okchois/Oilinwater/docs/hw/artwork-a5-r2-silk-logo-261003.md

# HMT500 A5-R2 실크 레퍼런스·두텍 로고 (2026-10-03)

## 바뀐 것

- 실제 PCB F.SilkS/B.SilkS와 거버에 반영. PDF에 번호를 덧씌우는 방식이 아니다.
- 표시 레퍼런스 **56 → 92/110개**. 부품 몸체 밖의 가까운 위치로 조정하고 혼동 가능 위치는 짧은 지시선(26개)을 사용했다.
- 기본 문자 폭/높이/선폭 **0.5/0.8/0.1 mm**. 혼잡 위치 22개는 **0.4/0.6/0.1 mm**로 축소.
- 탑면 J1 뒤쪽 빈 공간에 원본 **DOTECH 워드마크 폭 8.0 × 높이 1.34 mm**. 인쇄 가독성을 위해 작은 부제는 생략. 모델명은 로고 아래에 배치.
- 로고는 원본 알파 윤곽을 벡터로 변환한 실제 실크 다각형이다.
- 회로·부품 위치/면/회전·패드·배선/비아는 유지. 최신 LCSC 매칭 BOM/CPL을 새 거버 묶음에 포함.

## 검사

전체 재생성: 넷리스트 81/81 일치, DRC 오류 0, 미연결 0, 테스트 33개 통과.
실크 겹침 경고 0. **작은 글씨 높이 경고 22개** 및 기존 C44/D1 라이브러리 차이 경고 2개는 공개하고 유지한다.
이전 판과 배선/비아·패드의 형상/넷 및 부품 위치·회전·면 동일을 프로그램으로 대조했다.
탑/보톰 PDF는 실제 실크+마스크 개구+외곽이며, 보톰은 뒤집어서 읽는 방향이다.

## 남은 위험

**모든 레퍼런스를 실크로 표시한 것은 아니다.** 아래 18개는 가까운 공간에서 패드/몸체/다른 번호를 피하는 배치를 확보하지 못해 숨겼다:

D51, U13, U15, U2, C28, C4, C44, C45, C48, C50, C55, FB1, R14, R19, R31, R51, R52, R9

0.6 mm 적용 번호: D40, D41, L3, U1, U10, U9, C2, C21, C30, C41, C46, C5, C52, C57, GDT1, R11, R15, R17, R30, R33, R42, R8.

[JLC 고정밀 문자 안내](https://www.jlc.com/portal/q6i10417.html)는 최소 높이 0.8 mm·선폭 0.1 mm를 제시한다. 이번 0.6 mm 글씨는 그 권장 한계보다 작으므로 제조사 인쇄성 확인이 필요하며 선명한 인쇄를 보장하지 않는다. 일반 공정은 더 큰 글씨를 요구할 수 있다.

기존 0.15 mm 비아/POFV DFM, CPL 방향·재고, 제품 온도·몰딩·EMC 검증은 남아 있다. 이 자료는 제조 검토용이며 발주 승인이 아니다.

## 자료

- `manufacturing/jlc/artwork_A5_R2_review/`: 실제 거버·드릴, 현재 BOM/CPL, DRC/manifest.
- `hardware/kicad/artwork_metrics.json` 대신 프로젝트 폴더 `hardware/kicad/HMT500(260313A)/artwork_metrics.json`: 각 번호 좌표·크기·숨김 목록.
- 생성기 `silk_layout.py`, `artwork_finish.py`; 로고 원본/벡터는 `hardware/kicad/assets/`.
