okchois/Oilinwater/docs/hw/artwork-a4-261002.md

# HMT500 PCB A4 작업 결과

2026-10-02 · 회로 v0.10 / 기구 Rev I / PCB A4 · **미완성 검토용 — 제작·주문 불가**

## 바뀐 것

6층·신호 비아 축소 이후의 후속 배선을 수행했다. 미연결은 **A3 15건 → A4 5건**으로 줄었지만, 배선 완료 목표는 아직 달성하지 못했다. 기존 A1/A2/A3의 배치·배선 스냅샷은 보존했다. 회로의 부품 110개·넷 81개, 전원 12–28 V, VAO 16.1 V, 부하 조건 및 기구 외형은 변경하지 않았다.

- R42: 기구 좌표 x 44.925→45.475 mm, y 0.425→0.225 mm. GND 연결 및 DAC2 ISET 연결을 다시 배선했다.
- C6: x 18.650→18.600 mm. 최종 코트야드의 왼쪽 끝은 x 16.275 mm로 홀더 제한 x 16.250 mm를 만족한다. 초기 배치 시도에서 발견된 홀더 침범은 최종판에서 수정했다.
- R42 이동에 맞춰 MCU 반대면의 배치 탐색용 예약 창을 A4에서만 축소했다. A3 예약 창은 보존했다. 실제 패드·비아 간격 및 기구 배치 검사는 유지했다.
- eFuse UVLO·OVP·RTN 배선을 다시 정리했다. UVLO 인출 비아는 최종 KiCad 좌표 (108.500, 99.825) mm이다. CHASSIS 윗면 배선은 eFuse 옆에서 국부적으로 우회하며, 1.0 mm 간격을 유지한다.
- 고립된 GND와 3.3 V 구간을 연결했다. In2/In3에 디지털 영역의 3.3 V 폴리곤을 추가했다. In1/In4에는 신호 배선을 넣지 않았다.
- ADC PT_N과 인접 PT_SN_F 경로를 함께 조정했고 DAC 통신선 등 여러 신호를 재연결했다. 남은 막힌 경로는 아래 표와 그림에 표시했다.
- 신호 비아 0.30/0.15 mm 82개, 전체 관통 비아 220개이다. 기타 비아는 0.35/0.20, 0.40/0.20, 0.45/0.20, 0.70/0.40 mm이다. 블라인드·매립 비아는 사용하지 않았다.

## 확인한 것

| 검사 | 최종 결과 |
|---|---|
| 생성기부터 회로·PCB 재생성 | 성공, 종료 코드 0 |
| 넷리스트 | 81/81, 오류 0 |
| PCB 패드–넷 대조 | 오류 0 |
| 구리층 / GND 기준면 | 6층 / In1·In4 신호 배선 없음 |
| CREF·벅 SW/FB·DAC CMP 배선 길이 제한 | 통과 |
| 테스트 | 33개 통과 |
| KiCad 10.0.6 일반 DRC 오류 | 0 |
| **KiCad 미연결** | **5건 — 아래 상세** |
| DRC 경고 | 배선 끝 미연결 25건, 라이브러리 차이 2건 |
| 기구 조립 시뮬레이션 재실행 | 31항목: NG 0, WARN 1 |

DRC 경고는 제외하지 않았다. 라이브러리 차이는 기존 C44/D1의 실크를 Fab으로 옮긴 데서 발생한다. 배선 끝 경고와 미연결 항목은 별도의 집계다. 기구 WARN은 몰딩 유동/잔류 기포를 CAD로 보장할 수 없다는 항목이다. 이 결과는 원본 패드–넷 검사이며 KiCad의 네이티브 회로도 대조 오류 0을 주장하는 것은 아니다.

## 남은 위험

**전원 VIN_P와 RS-485 A, SWCLK, OUT1_SGOOD가 완전히 연결되지 않았다. 따라서 정상 동작 또는 제작 가능 상태가 아니다.** 임시 점퍼, ERC/DRC 제외 규칙, GND 기준면 침범으로 미연결을 숨기지 않았다.

| 미연결 | 의미 / 다음 처리 |
|---|---|
| VIN_P 1건 | eFuse 출력 측과 VAO 벅 입력 측 전원 연결. MCU/DAC 중앙 구간에서 전원 통로를 먼저 확보해야 한다. |
| RS485_A_EXT 2건 | U11 A핀–D60 TVS–J1 사이의 세 구간이 분리되어 있다. U11/D60 인출과 커넥터 방향 경로를 함께 수정해야 한다. |
| SWCLK 1건 | MCU U4.36–SWD J2.4 연결. MCU 우측 핀 탈출과 기존 비아 위치를 재검토해야 한다. |
| OUT1_SGOOD 1건 | 보호 IC U9.8–MCU U4.11 연결. MCU 왼쪽 탈출부와 반대면 DAC 주변의 배선 여유가 필요하다. |

단순 우회·주변 배선 제거 후 복원·배선 잠금 해제 등을 시험했으나 위 5건을 모두 해소하지 못했다. 연결 수가 다시 늘거나 간격 오류가 생긴 시험판은 최종판으로 채택하지 않았다. 이후 작업은 막힌 부품 인출부의 배치와 주변 경로를 함께 바꾸어야 한다. 다음 작업자에게 이 5건을 넘긴 것이 완료를 의미하지 않는다.

- SMD 패드와 비아 외경의 겹침을 보수적인 패드 경계 상자로 검사한 **POFV 후보는 22개**다. 모두 홀 0.20 mm 이상이며, 0.15 mm 홀 후보는 0개다. 실제 마스크·페이스트·제조 공정 확인은 별도로 필요하다. `POFV_candidates.csv`에 좌표를 기록했다.
- JLC 공개 POFV 범위는 홀 0.20–0.50 mm, 권장 환형 링 0.075 mm이다. [JLC 공식 POFV 안내](https://jlcpcb.com/news/free-via-in-pad-6-20-layer-pcbs-pofv). **0.15 mm 일반 비아와 0.20 mm POFV 혼용의 최종 제조 수락·가격은 확인 필요**이며 현재 파일만으로 해당 공정을 주문한 상태는 아니다.
- RTN 채움 구리의 계산 면적은 F.Cu 약 19.01 mm², B.Cu 약 20.05 mm²다. 패드/배선 자체의 구리까지 합산한 열 모델이 아니므로 방열 성능 보장에 사용할 수 없다. eFuse 시동·고장·최고 온도 시험이 필요하다.
- 배선 연결을 모두 마친 뒤 전원·서지 경로의 좁아진 곳, GND 귀환 경로, AO 발열, 디커플링 루프를 검토해야 한다. 일반 DRC 오류 0만으로 전기 성능 검수를 마친 것은 아니다.
- 제조 DFM·최종 적층 두께·BOM 미확정 2줄·CPL 회전·실장 공정은 주문 전에 확인해야 한다. 거버와 JLC 주문 패키지는 발행하지 않았다.

## 내가 결정할 것

이번 6층·비아 축소 작업은 이미 승인받은 범위이며 추가 승인을 요구하지 않는다. 현재는 주문 승인 단계가 아니다. 기존 제품 온도·몰딩 재료 등의 미결 사항은 결정 기록을 유지한다.

## 재현

`hardware/kicad/rebuild_artwork.sh`의 기본은 A4다. `placement/artwork_A4.json`과 `routing/artwork_A4_draft.json`이 배치·배선의 입력이며, 층수나 배치가 다르면 스냅샷 복원을 거부한다. 이전 판은 HMT_ARTWORK=A1/A2/A3로 지정한다. 검토 묶음에는 생성기·라이브러리·회로/PCB·검사 결과를 포함했다. 데이터시트 PDF는 포함하지 않았다.

## 미연결 상세 — KiCad 좌표 mm

| # | 넷 | 시작 | 끝 |
|---|---|---|---|
| 1 | OUT1_SGOOD | 배선 [OUT1_SGOOD] on B.Cu, 길이 0.8202 mm (135.337, 106.175) | 패드 11 [OUT1_SGOOD]의 U4 위F.Cu (124.138, 102.250) |
| 2 | SWCLK | 패드 36 [SWCLK]의 U4 위F.Cu (132.463, 97.250) | 배선 [SWCLK] on F.Cu, 길이 0.1414 mm (107.850, 97.000) |
| 3 | RS485_A_EXT | 패드 6 [RS485_A_EXT]의 U11 위F.Cu (117.025, 106.200) | 배선 [RS485_A_EXT] on B.Cu, 길이 0.2750 mm (116.575, 107.000) |
| 4 | RS485_A_EXT | 배선 [RS485_A_EXT] on B.Cu, 길이 0.6500 mm (118.525, 107.275) | 패드 3 [RS485_A_EXT]의 J1 위F.Cu (139.650, 101.875) |
| 5 | VIN_P | 배선 [VIN_P] on B.Cu, 길이 1.0645 mm (133.700, 107.640) | 배선 [VIN_P] on In2.Cu, 길이 0.1750 mm (118.325, 101.750) |
