okchois/Oilinwater/docs/hw/ao-tvs1401-261001.md

# AO TVS1401 변경 — 회로도 v0.10 / 결정 #41

사용자 지시에 따라 D30/D40만 TVS3301DRBR → TVS1401DRBR로 변경했다. 입력 D2, RS-485 D60/D61은 33 V 부품을 유지한다. VAO 16.1 V, TPS26611, 10 Ω 직렬 저항, 출력 부하 ≤500 Ω 및 최대 24 mA는 유지한다.

- 정상 부하 단자전압: 24 mA × 500 Ω = 12 V. 0–10 V 출력과 함께 ±14 V 스탠드오프 범위 안이다. 14 V는 정확한 클램프 전압이 아니다.
- TI SLVSEQ2B §8.6: 30 A, 8/20 µs에서 클램프 전형 20.5 V / 최대 22.2 V(27°C, 초기 0 V), 최대 23.55 V(125°C, 초기 ±14 V).
- 단순 검산: DAC측을 +16.1 V로 가정하고 단자 −23.55 V이면 TPS26611 양단은 39.65 V. ±55 V 절대최대보다 낮지만 VAO 공차·IN측 순간전압·배선 오버슈트·파형/전류/온도는 별도 확인해야 한다. 실제 서지 시험 통과를 뜻하지 않는다.
- IN 핀 1–4, GND 5–8. 노출 중앙 패드는 반드시 FLOAT. 기존 Texas_DRB0008A_PadFloat 풋프린트를 유지한다.
- **AO 단자에 외부 ±28/30 V 지속 인가 무손상 보장은 제외한다.** 외부 전원→TVS→GND 경로는 TPS26611 및 10 Ω 바깥에 있어 이 부품들이 그 전류를 차단하지 못한다.
- 출력 개방 시 DAC의 컴플라이언스 전압 상승으로 TVS가 연속 도통할 수 있다. 24 mA 개방 상태의 TVS 온도·SGOOD/DAC 경보·펌웨어 개방 검출을 시험해야 한다. 보호가 개방 검출에 미치는 영향도 확인 필요.
- LCSC C1849891로 BOM을 분리했다. JLC 조립 등급·재고·가격은 주문 시 확인 필요.

근거: [TI TVS1401 데이터시트](https://www.ti.com/lit/ds/symlink/tvs1401.pdf), [LCSC C1849891](https://www.lcsc.com/product-detail/C1849891.html). 제조사 PDF는 커밋하지 않았다.

검증: AGENTS §5 재생성 순서 완료, unittest 33개 모두 통과, 넷리스트 81/81 오류 0. PCB 부품 배치 좌표 유지. D30/D40 TVS1401 2개(C1849891), D2/D60/D61 TVS3301 3개(C2864392)로 BOM 분리 확인. DRC 간격·코트야드 오류 0. 기존 실크/라이브러리 항목 426, 미연결 327(배선 전)은 남아 있다. PCB/넷리스트 재생성은 Mac KiCad 10.0.6으로 수행했다. 회로도 표제란 v0.10 및 AO 오결선 보장 제외 주석을 PDF에서 확인했다.
