okchois/Oilinwater/docs/hw/mcu-selection.md

# MCU 선정 검토 — HMT500

작성일: 2026-09-26 · 상태: **결정 — STM32G0B1CCT3** (샘플 단계는 JLC 부품 CCT6, 결정 #39 — 양산 전 온도 사양으로 재확인) (2026-09-26, 사내 사용 부품 우선 방침). T3 견적 확인 대기

현재 회로도는 STM32L431RCT6(LQFP64, −40~85 °C)입니다. 이 문서는 "이 칩이 최선인가"를 요구사항부터 다시 따져 봅니다. 끝에 다른 AI 도구(Codex CLI 등)나 외부 검토자에게 그대로 넘길 수 있는 질문지를 붙였습니다.

> 표의 가격과 온도 등급은 공개 자료와 기억에 기댄 값입니다. **대리점 견적과 데이터시트로 반드시 확인**해야 합니다. "확인 필요" 표시가 붙은 항목은 특히 그렇습니다.

## 0. 두텍 MCU 사용 이력 (구매현황 2023-09 ~ 2026-09 기준)

| 부품 | 코어 | 적용 제품 | 구매 경로 | 단가 수준 (참고) |
|---|---|---|---|---|
| STM32F412RET6 | M4F 100 MHz, 512 KB | HPX3000 | Mouser | 약 9,200~9,900원 |
| STM32G071CBT6 (LQFP48) | M0+ 64 MHz, 128 KB | PSU750, GTX500 | Mouser | 약 3,300~3,600원 |
| **STM32G0B1CCT6 (LQFP48)** | M0+ 64 MHz, **256 KB** | **DP2000** | **국내 대리점**, Mouser | **약 2,060원 (100개, 국내)** |
| STM32G031K6T6 (LQFP32) | M0+ 64 MHz, 32 KB | GTX30P | Mouser | 약 2,600원 |
| STM32L011F3/F4U6 | M0+ 32 MHz, 8/16 KB | HTP1100W | DigiKey | 약 1,200원 |
| (STM32F103VET6) | M3 | 구매현황 제목에만 있음, 기간 내 구매 행 없음 | — | — |

**정리:** 두텍은 STM32만 쓰고, 특히 **G0 계열(G031, G071, G0B1)** 을 여러 제품에 쓰고 있습니다. L4와 G4는 쓴 적이 없습니다. M4F는 F412를 HPX3000에 씁니다. **STM32G0B1CC는 같은 부품을 DP2000에 쓰고 있고 국내에서 사고 있어서**, 개발 도구, 드라이버, 생산 기록 지그, 재고를 함께 쓸 수 있습니다.

## 1. MCU가 해야 할 일 (요구사항)

| # | 요구 | 근거 | 필수/선호 |
|---|---|---|---|
| R1 | SPI 1개, 칩 선택 4개 (PCAP04, ADS1220, DAC8760 ×2) | 회로 설계서 6절 | 필수 |
| R2 | UART 1개 + RS-485 방향 제어(DE). 하드웨어 DE면 더 좋음 | Modbus RTU 3.5문자 간격, 부트로더 | 필수 (HW DE는 선호) |
| R3 | GPIO 약 20개 (인터럽트 2, 알람·고장 입력 5, LED 1, SWD 2 포함) | 핀 할당표 | 필수 |
| R4 | 플래시 ≥ 128 KB, 가능하면 256 KB. 페이지 단위 소거 | 부트로더 32K + 앱 + 설정 + 교정 | 필수 |
| R5 | 실수 연산: ppm = aw × 10^(A + B/T), 5계수 모델, 교정 다항식 | 측정 주기 약 1 Hz | 선호 (아래 참고) |
| R6 | **동작 온도 −40~105 °C 이상**, 가능하면 125 °C | 오일 최대 120 °C, 전자부 발열 약 1.3 W | 필수 (열해석 후 확정) |
| R7 | 작은 패키지 (7×7 이하) | PCB 폭 23 mm, 한 면 높이·면적 제한 (기구 Rev C) | 선호 |
| R8 | 워치독, 저전압 리셋, 하드웨어 CRC | 현장 무인 동작, 부팅 시 이미지 검증 | 필수 (CRC는 선호) |
| R9 | 국내 수급, 10년 이상 공급, 두텍 개발팀 경험 | 양산·유지보수 | 필수 |
| R10 | 단가 (1k 기준) | 전자부 BOM $36~64 목표 | 선호 |

**R5 다시 보기:** 측정 주기가 약 1 Hz라서 FPU가 꼭 필요하지는 않습니다. FPU 없는 Cortex-M0+도 소프트웨어 실수 연산으로 1초에 한 번 계산하는 데는 충분합니다(코드가 수 KB 늘어나는 정도). 처음 선정 이유에서 "FPU가 필요하다"는 말은 과했고, "있으면 편하다"가 정확합니다.

## 2. 후보 비교

| 후보 | 코어 / 클럭 | 플래시 | HW RS-485 DE | 125 °C 등급 | 패키지 (작은 것) | 단가 감 (1k) | 비고 |
|---|---|---|---|---|---|---|---|
| **STM32L431CC** (현재 계열, 48핀) | M4F / 80 MHz | 256 KB, 2 KB 페이지 | 있음 (USART DEM) | 접미사 3/7 있는지 **확인 필요** | UFQFPN48 7×7, LQFP48 | 약 $2~3 | 부트로더 맵·핀표 그대로 사용. 가장 적은 변경 |
| STM32G491CE/CC (2A절) | M4F / 170 MHz | 512 / 256 KB | 있음 | **있음 (CET3·CEU3 판매 확인)** | LQFP48, UFQFPN48 7×7 | 약 $5~6 (100개) | 요청 후보. 125 °C 확실, 가격 약 2배 |
| STM32G431CB | M4F / 170 MHz | 128 KB | 있음 | 있음 (접미사 3, **확인 필요**) | UFQFPN48 7×7 | 약 $3~4 | 성능 과잉. 125 °C가 꼭 필요하면 후보 |
| STM32G0B1CB / G071 | M0+ / 64 MHz | 128 KB | 있음 | 있음 (접미사 3, **확인 필요**) | UFQFPN48, LQFP48 | 약 $1.5~2.5 | FPU 없음 (R5는 소프트웨어로 해결). 원가 절감 1순위 |
| STM32U0 / U3 계열 | M0+ / M33 | 64~256 KB | 있음 | **확인 필요** | 작은 패키지 다수 | **확인 필요** | 신규 계열. 수급·장기 공급 확인 필요 |
| TI MSPM0G3507 | M0+ / 80 MHz (수학 가속기 MATHACL) | 128 KB | **확인 필요** | 있음 (−40~125 °C) | VQFN32/48 | 약 $1 안팎 | 저가·고온. TI 부품(DAC8760, THVD2450)과 한 대리점. 툴체인 경험 확인 필요 |
| Renesas RA4M1 / RA2L1 | M4F / M23 | 256 KB | **확인 필요** | 제품별 상이 | LQFP48 | 약 $2~3 | 국내 지원 있음. 선택 이유가 약함 |
| GigaDevice GD32 (STM32 호환) | M4F 등 | 다양 | 있음 | 제품별 상이 | 다양 | 저가 | 호환성·장기 공급·품질 문서가 약함. 산업용 계측기에는 비추천 |

## 2A. 요청 후보: STM32G491CET3 상세 검토

주문 코드 해석: G491 · **C** = 48핀 · **E** = 플래시 512 KB · **T** = LQFP48 7×7 · **3** = −40~125 °C (접합 130 °C).

| 항목 | STM32G491CET3 | STM32L431CC (비교) | HMT500에서 의미 |
|---|---|---|---|
| 코어 | Cortex-M4F 170 MHz, CORDIC·FMAC 가속기 | Cortex-M4F 80 MHz | 둘 다 충분. 성능은 G491이 과잉. CORDIC은 지수·로그 계산에 쓸 수 있지만 필요하지는 않음 |
| 플래시 / RAM | 512 KB / 112 KB | 256 KB / 64 KB | 512 KB면 **A/B 두 이미지 업데이트**(실패 시 이전 펌웨어로 복귀)가 가능. 지금 부트로더 맵(256 KB)도 그대로 들어감 |
| 플래시 페이지 | 2 KB (카테고리 4, 단일 뱅크), 64비트 단위 기록 | 2 KB, 64비트 단위 기록 | **부트로더 포팅이 거의 같음** (`bl_port.h` 함수 3개) |
| 온도 등급 | **125 °C 등급이 실제 판매 중** (CET3, CEU3 확인) | 계열 데이터시트에는 125 °C 범위가 있으나 CC 48핀의 3/7 접미사 판매 여부는 **확인 필요** | **G491의 가장 큰 장점** |
| USART / RS-485 DE | USART 3 + LPUART, 하드웨어 DE 있음 | 있음 | 같음 |
| 아날로그 | 12-bit ADC ×2, DAC ×4, OPAMP, 비교기, CAN-FD | ADC ×1, DAC ×2, OPAMP | 이 제품에서는 대부분 안 씀 (측정은 PCAP04·ADS1220, 출력은 DAC8760) |
| 소비 전류 | 170 MHz 동작 시 수십 mA (클럭을 낮추면 줄어듦) | 저전력 계열 | 외부 전원이라 문제는 아님. 3.3 V LDO 여유와 발열만 확인. 16~48 MHz로 돌리면 충분 |
| 패키지 | LQFP48 7×7 (CET3), UFQFPN48 7×7 (CEU3) | 같음 | 폭 23 mm PCB에 들어감 |
| 가격 (참고) | RS 100개 기준 약 SGD 8.5 / HK$ 50 (약 $6.3) | 약 $2~3 | 1k 견적은 대략 **$2~3 비쌀 것**으로 예상. 대리점 확인 필요 |

**평가**

- **장점:** 125 °C 등급을 확실히 구할 수 있습니다. 오일이 120 °C일 때 전자부 온도가 85~105 °C를 넘을 수 있다는 위험을 칩 선정 단계에서 없앨 수 있습니다. 부트로더와 드라이버는 L4와 거의 그대로 쓸 수 있습니다(같은 STM32 HAL, 같은 2 KB 페이지).
- **단점:** 가격이 약 2배이고, 170 MHz와 풍부한 아날로그 기능 대부분을 쓰지 않습니다.
- **변형안:** 512 KB가 필요 없으면 **STM32G491CC(256 KB)** 의 125 °C 등급이 더 쌀 수 있습니다(주문 코드와 가격 확인 필요). A/B 두 이미지 업데이트를 원하면 CE(512 KB)를 유지합니다.

## 3. 현재 판단 (교차 검토 전)

**(최종 갱신 — 구매 이력 반영) 1순위: STM32G0B1CCT3** (M0+ 64 MHz, 256 KB, 144 KB RAM, LQFP48, −40~125 °C)
   - DP2000에서 쓰는 G0B1CCT6과 같은 칩의 125 °C 등급입니다. 핀·코드·툴체인·생산 지그가 같습니다.
   - 플래시 256 KB, 2 KB 페이지, 64비트 단위 기록이라 **부트로더 메모리 맵(32K + 208K + 8K + 8K)을 그대로** 씁니다. 단, 256 KB판은 뱅크 2개(각 64페이지)라서 뱅크 2의 페이지 번호 지정과 "이중 뱅크 + 프리페치" 에라타를 부트로더 포팅 때 확인합니다.
   - FPU가 없지만 1 Hz ppm 계산은 소프트웨어 실수 연산으로 충분합니다(R5).
   - USART 하드웨어 DE, IWDG, BOR, 하드웨어 CRC가 모두 있습니다.
   - 가격: T6이 국내 약 2,060원(100개)입니다. T3(125 °C)은 이보다 조금 비쌀 것으로 보이며, **국내 대리점에 T3 견적과 재고를 확인**해야 합니다.
   **2순위: STM32G491CET3** — FPU·성능 여유가 필요하거나 A/B 이중 이미지(512 KB)를 원할 때. 두텍은 G4를 써 본 적이 없고 가격이 약 3배입니다.
   **제외: STM32L431** — 두텍 사용 이력이 없고 G0B1 대비 이점이 FPU뿐입니다.

이전 판단 (구매 이력 반영 전):

0. **(갱신) 고온 조건이 확정되거나 L431CC 고온 등급을 구하기 어려우면 STM32G491CET3(또는 CC 256 KB판)를 1순위로 합니다.** 125 °C 등급이 판매 중인 것이 확인되었고, 설계 변경은 L431CC와 비슷하게 적습니다.
1. **추천: STM32L431CC 48핀으로 바꾸기.** 단, 105 °C 또는 125 °C 등급을 구할 수 있을 때만입니다.
   - 부트로더 메모리 맵, 하드웨어 DE, CRC, 핀 할당이 그대로라 설계 변경이 가장 적습니다.
   - 64핀 → 48핀으로 PCB 면적이 약 절반이 됩니다.
2. **L431의 고온 등급을 구할 수 없으면:** STM32G0B1(원가) 또는 STM32G431(성능) 중에서 고릅니다. 둘 다 125 °C 등급이 있는 것으로 알고 있으나 확인이 필요합니다.
   - G0: FPU가 없고 플래시가 128 KB라 부트로더 맵을 128 KB에 맞게 다시 짜야 합니다(부트로더 16~24K + 앱 ~96K).
3. **원가를 가장 중시하면:** TI MSPM0G3507을 평가해 볼 가치가 있습니다. UART의 RS-485 하드웨어 DE 지원 여부와 두텍의 개발 경험이 관건입니다.

**가장 큰 결정 요인은 두텍이 이미 쓰는 MCU 계열입니다.** 기존 제품이 STM32라면 STM32 안에서 고르는 것이 개발·생산·유지보수 모두 유리합니다.

## 4. 교차 검토 질문지 (Codex CLI 등에 그대로 전달)

아래 블록을 그대로 복사해 넘기면 됩니다. 저장소 전체를 볼 수 있는 도구라면 파일 경로도 함께 읽도록 합니다.

```text
역할: 산업용 계측기 하드웨어 설계 검토자.

제품: DOTECH HMT500 오일 내 수분 트랜스미터 (E+E EE364급).
- 측정: IST MK 정전용량 습도소자 → PCAP04 (SPI), Pt1000 → ADS1220 (SPI)
- 출력: DAC8760 ×2 (SPI, 전압/전류 선택), RS-485 Modbus RTU (THVD2450)
- RS-485로 펌웨어를 업데이트하는 자체 부트로더 (플래시 맵: BL 32K, 앱 208K, 설정 8K, 교정 8K, 2 KB 페이지)
- 계산: ppm = aw × 10^(A + B/T), 약 1 Hz
- 전원 12~28 V (v0.8), 전자부 발열 약 1.3 W, 오일 온도 최대 120 °C
- PCB: 57 × 23 mm 1장, 원통 하우징 안. 부품 높이 한 면 5~12 mm
- 참고 파일: docs/hw/mcu-selection.md, docs/hw/hardware-block-design.md,
  docs/hw/circuit-design.md, docs/rs485-bootloader-design.md, firmware/bootloader/

현재 선택: STM32L431RCT6 (LQFP64, −40~85 °C). 검토안: STM32G0B1CCT3 (1순위, 회사가 DP2000에 G0B1CCT6 사용 중, 국내 구매), STM32G491CET3 (2순위), STM32L431CC.
회사 사용 이력: STM32만 사용 (F412, G071, G0B1, G031, L011). L4·G4 사용 이력 없음.

질문:
1. 위 요구사항에 대해 STM32L431이 최선인가? 더 나은 후보가 있다면 이유와 함께.
2. STM32L431CC의 105 °C/125 °C 등급(주문 코드 접미사 7/3) 실제 존재 여부와 패키지.
3. STM32G0B1CCT3, STM32G491CET3(또는 G491CC), TI MSPM0G3507과 비교해 원가·고온·RS-485 하드웨어 DE·플래시 구조·장기 공급 측면의 장단점.
4. FPU 없는 코어로 1 Hz ppm 계산과 5계수 모델을 처리할 때의 실제 부담.
5. 이 요구사항에서 놓친 MCU 관련 위험(ESD, 클럭 정확도와 Modbus 보레이트, 플래시 내구성, 부트로더 안전성 등).
답은 표 하나와 추천 1순위·2순위로 정리하고, 확신이 낮은 사실은 "확인 필요"로 표시할 것.
```

## 5. 결정 후 바꿀 곳

- 회로도: `hardware/kicad/gen_hmt500.py` (MCU 심볼·핀), 넷리스트 재검증
- 핀 할당: `docs/hw/circuit-design.md` 6절
- 부트로더 메모리 맵: `docs/rs485-bootloader-design.md` 3절, `firmware/` (플래시 크기가 바뀔 때만)
- 부품표·원가: `docs/hw/bom.csv`, `docs/hw/bom-cost.md`
- 기구 3D의 MCU 크기: `hardware/mech/hmt500_params.py` `PCB_PARTS`

## 참고 자료

- STM32G0B1CC 데이터시트 (−40~125 °C 등급 포함): https://www.st.com/resource/en/datasheet/stm32g0b1cc.pdf
- STM32G0B1 이중 뱅크·프리페치 에라타 논의: https://community.st.com/stm32-mcus-products-25/dual-bank-issue-on-stm32g0b1rct6-26786
- STM32G491CET3 가격: RS Online https://sg.rs-online.com/web/p/microcontrollers/0330260 , https://hkcn.rs-online.com/web/p/microcontrollers/0330260
- STM32G491CEU3 (125 °C, QFN): https://estore.st.com/en/stm32g491ceu3tr-cpn.html , Mouser https://www.mouser.com/ProductDetail/STMicroelectronics/STM32G491CEU3?qs=CiayqK2gdcKP%2BMERfRJ0Dg%3D%3D
- STM32G491 플래시 구성(카테고리 4, 2 KB 페이지): https://community.st.com/t5/stm32cubeide-mcus/stm32g491-flash-memory-organization/td-p/696784
- STM32G491 데이터시트 DS13122: https://www.st.com/resource/en/datasheet/stm32g491cc.pdf
- STM32L431 데이터시트 (온도 범위): https://www.st.com/resource/en/datasheet/stm32l431cb.pdf
