okchois/Oilinwater/docs/hw/external-review-response-260930.md

# 외부 회로 검수(2026-09-30) 대응 — HMT500(260313A) 회로도 v0.9

검수 대상: `HMT500(260313A)_schematic.pdf` 8쪽 (2026-09-30 오전 판, SHA-256 8146…edca).
두텍 지시: "맞는 것·동의하는 것을 반영" (결정 #35).

검수 PDF 이후 이미 바뀐 것: C22 220 → 330 pF (결정 #33), L2 XGL4030-153 → XGL4040-153MEC, D50 제조사 확정 (결정 #34).

## 1. 항목별 판단과 조치

| ID | 판단 | 조치 (이 저장소) |
|---|---|---|
| H01 음(−) 서지 때 eFuse IN–OUT | 맞음 | **회로 수정:** D2 뒤·U1 앞 직렬 쇼트키 **D3 PMEG10010ELR-QX** (100 V 1 A, 누설 150 nA, LCSC C5361358). D2가 −42.5 V로 잡는 동안 VIN_P +28 V → 약 71 V를 D3가 받음 (100 V 정격). U1 IN은 음전압을 받지 않음. 손실 약 0.45 V × 0.1 A. U1 입력 넷 이름 = VIN_D. UVLO·OVP는 입력 단자 기준 약 +0.45 V 이동 (UVLO ≈ 9.3 V, OVP ≈ 33.1 V — 입력 DC 절대 최대 33 V는 그대로) |
| H02 RS-485 ±1 kV 서지 | 맞음 | **회로 수정:** A·B–GND에 **TVS3301 D60/D61** (±33 V 동작 → ±30 V 오결선 도통 안 함, 최대 42.5 V @ 27 A < THVD2410 ±70 V). 1 kV / 42 Ω 결합 → 최대 약 24 A. U11을 **THVD2410DGKR (VSSOP-8, 핀 배정 같음, LCSC C1858306)** 로 바꿔 자리 확보 |
| H03 보호기 차단 후 피드백 끊김 | 맞음 (조건부) | **회로 추가 (결정 #37, IVS320 AO rev 1.0 방식):** DAC CMP 보상 VOUT–CMP 4.7 nF + CMP–GND 100 pF (SBAS528D 8.3.2), DAC 출력 클램프 BAS70-04 (D41/D51, GND − 0.3 ~ AVDD + 0.3 V). + 펌웨어 F1–F2, 시험 T3 |
| H04 +Vs 클램프 공차 | 부분 동의 → **해소 (결정 #37)** | **최종:** 제너 폴로워(Q1·R50·D50) 삭제, **+Vs = VAO 16.1 V 벅 고정** (15.5–16.6 V, 권장 30 V까지 13 V 여유). _이전 단계(결정 #35): D50 27 V → BZX84C24LT1G_ (22.8–25.6 V, LCSC C43728). VS ≈ 23.4 V, 최악(상한 + 85 °C 드리프트 − VBE) ≤ 26.4 V → +Vs 권장 30 V까지 여유 3.6 V. 하한(−40 °C, 저전류) 약 19.7 V → 출력 단자 최대 전압 사양에 반영 (2절) |
| H05 L2 품번 없음 | 맞음 | 이미 해결 (XGL4040-153MEC, 결정 #34) |
| H06 12 V 허용 부하 | 맞음 | 사양 표 2절 |
| H07 입력 전류·발열 예산 | 맞음 | 예산 표 3절, 펌웨어 F3 |
| H08 IDAC ≤ 250 µA 문구 | 맞음 | 회로도 문구 → "IDAC = 250 µA 고정" |
| H09 전원 OFF 역급전 | 동의 (위험 낮음) | 시험 T6 |
| H10 센서·출력 정확도 | 맞음 | 펌웨어 F5 (PCAP04 구동 주파수), 정확도 예산 4절 |
| H11 온도 등급·기동·고장 복귀 | 맞음 | 5절 (제품 온도 사양 미정 → 두텍 결정 필요), 펌웨어 F4, F6 |

**자리 확보:** 새 부품 3개(D3, D60, D61)를 넣을 자리가 없어 ① U11을 VSSOP로, ② C7(VIN_P 2.2 µF 100 V 1210)을 빼고, ③ 저전압 R·C 37개를 0603 → 0402(LCSC 대부분 Basic)로 바꿨습니다. 100 nF 디커플링(16 V X7R), 1 µF(10 V X7R, 5 V 이하 넷), 22 nF, 20 pF C0G, 10 k/100 k/1 k/10 Ω 저항(50 V). VS_CLAMP(약 24 V) 콘덴서 C46/C53/C56과 정밀·고전압 부품은 0603 이상 유지. 결과: 104개 전부 배치, RS-485 TVS는 U11 A/B 핀에서 1.4–2.5 mm, D3는 U1에서 3.7 mm. C7은 D3가 음의 서지를 막아 VIN_P를 붙잡아 둘 이유가 없어져 뺐고, 벌크 C5 10 µF와 C43 4.7 µF는 그대로입니다.

## 2. 아날로그 출력 허용 부하 (H06) — 제품 사양 초안

가정: 입력 직렬 손실 R1 4.7 Ω + L1 2 × 0.31 Ω + D3 0.45 V, DAC AVDD 직렬 10 Ω, 전류 출력 헤드룸 2 V (DAC8760), TPS26611 RON 최대 12.5 Ω + R30/R40 10 Ω, TPS26611 단자 전압 < +Vs.

| 입력 전압 | VIN_P (추정) | 24 mA 최대 부하 (계산) | 20 mA 최대 부하 (계산) | **사양 (여유 포함)** |
|---|---|---|---|---|
| 12 V | 약 11.1 V | 약 340 Ω | 약 410 Ω | ≤ 250 Ω (아래 식) |
| 18 V | 약 17.2 V | 약 600 Ω | 약 720 Ω | **≤ 500 Ω** |
| 24–28 V | 약 23.2 V 이상 | 약 790 Ω (+Vs 최악 하한 19.7 V가 한계) | 약 950 Ω | **≤ 500 Ω** |

**결정 #37 이후 (AVDD = VAO 16.1 V):** 전원 ≥ 18 V에서 VAO 최소 15.5 V → AVDD 15.2 V → 24 mA 최대 부하 약 528 Ω (≥ 500 Ω 사양 만족, 여유 작음 → 시험 T3). 12 V 입력은 벅이 최대 듀티로 VAO ≈ 10.8 V, AVDD ≈ 10.5 V → 24 mA 약 330 Ω (사양 250 Ω 만족). **0–10 V 전압 출력은 AVDD ≥ 10.5 V 필요 (SBAS528D 표 7) → 12 V 입력에서 경계 — 전압 출력 0–10 V는 전원 ≥ 13 V 권장**으로 사양에 표기.

**확정 사양 (결정 #36, 경쟁사 EE364·MMT162·MMT330과 같은 표기):** 전원 **12–28 V DC (최대 28 V)**, 전류 출력 부하 **RL ≤ 500 Ω** (전원 ≥ 18 V). 18 V 미만은 **RL ≤ (V+ − 6 V) / 24 mA** (12 V → 250 Ω). 계산 한계(24 V 약 790 Ω)보다 여유를 둔 값이며 시험 T3으로 확인. 입력 DC 절대 최대 33 V는 손상 한계로 유지 (동작 범위 아님).

- 전압 출력(0–5 / 0–10 V): 최소 부하와 12 V 입력에서 0–10 V 헤드룸은 DAC8760 데이터시트 값으로 확인 후 표에 넣음 (확인 필요). 시제품 시험 T3에서 측정.
- 입력 DC 절대 최대 33 V (TVS3301), 정상 12–28 V.

## 3. 입력 전류·발열 예산 (H07)

| 부하 | 12 V 입력 | 28 V 입력 | 근거 |
|---|---|---|---|
| 출력 2채널 (24 mA + DAC AVDD 약 3.5 mA + OPA197 약 1.1 mA) × 2 | 약 57 mA | 약 57 mA | VIN_P에서 바로 |
| 3.3 V 부하 (MCU 약 8, RS-485 송신 54 Ω 약 36, 측정부·기타 약 4) 약 48 mA → 5 V 벅 (효율 85 %) | 약 25 mA | 약 10 mA | 5.0 V × 48 mA / 0.85 / VIN_P |
| 전원 감시·TPS26611 (결정 #37 후: 출력부는 VAO 벅 경유 — 28 V에서 입력 전류 약 41 mA로 감소) | 약 1.5 mA | 약 1.5 mA | |
| **합계 (최악: 두 출력 24 mA + RS-485 연속 송신)** | **약 84 mA** | **약 69 mA** | eFuse 제한 148.9 mA (저전류 공차는 확인 필요, ±20 % 가정 시 최소 119 mA) → 여유 ≥ 35 mA |

- 발열 최악: 28 V, 두 출력 24 mA, 단자 단락 → 채널당 약 0.66 W (대부분 DAC), 합계 약 1.3 W + 전원부 약 0.3 W. 몰딩 시제품 온도 시험(미결 항목 "DAC 발열")으로 판단.
- UVLO(입력 약 9.3 V) ~ DAC 최소 전원 사이에서는 MCU만 동작 → 펌웨어 F3.

## 4. 정확도 예산에 넣을 항목 (H10)

- R32/R42 ISET 15 k 0.1 % 25 ppm/K: 교정 후에도 온도 드리프트 최대 약 0.25 % / 100 K (전류 출력 오차 항목).
- Pt1000 2선: 배선 왕복 1 Ω ≈ 0.26 °C. 1회 영점 교정 후에도 하네스 온도 변화분은 남음.
- C22 330 pF C0G ±2 % (LCSC): 절대값은 교정으로 제거, C0G라 온도 변화 작음.

## 5. 제품 온도 사양 (H11) — 두텍 결정 필요

- 부품 최저 등급: **GDT1 Bourns 2035 −55~+85 °C**, JST SH/GH −25~+85 °C (카탈로그, 확인 필요). MCU T3·PCAP04·X7R은 125 °C.
- 결정 필요: 주위 온도 범위, 오일 최고 온도(120 °C)에서 **전자부(몰딩 안) 최고 온도**. 85 °C를 넘으면 GDT·JST 대체품 필요.

## 6. 펌웨어 필수 요구 (검수 반영)

| ID | 요구 | 근거 |
|---|---|---|
| F1 | SGOOD(PA0/PA4)가 High(고장)이면 해당 채널 DAC 출력 끄기(OUTEN = 0) 또는 설정값 유지. 복귀 시 DAC 슬루 제한(SREN) 켜고 천천히 목표값으로 | H03 전압 모드 포화 → 재연결 과도 방지 |
| F2 | 전압 모드 단락·오결선 해제 후 파형으로 슬루 설정값 확정 (시험 T3) | H03 |
| F3 | VIN_SENSE(PB0)로 입력 전압 감시: DAC 최소 전원 미만이면 출력 무효 표시(NAMUR 고장 전류 또는 알람), 히스테리시스 두고 복귀 | H07 |
| F4 | DAC 초기화: 전원 안정 후 리셋 → 출력 비활성 상태에서 설정(REXT = 1, SPI2 모드 3, LATCH 타이밍) → 출력 켜기. 통신 끊김·IWDG 리셋·UVLO 때 출력값 정책을 사양으로 정의 | H11 |
| F5 | ADS1220 IDAC = 250 µA 고정. PCAP04 센서 구동 주파수 약 10 kHz (MK33-W 권장, 확인 필요) | H08, H10 |
| F6 | HSI16 온도 오차: 부팅 첫 프레임부터 UART 허용 오차 만족 확인, 보정 방식 구현·시험 | H11 |

## 7. 시험 계획 추가 (시제품)

| ID | 시험 | 합격 기준 |
|---|---|---|
| T1 | 입력 음(−) 서지: 28 V·경부하·출력 충전 상태, U1 IN–OUT, IN–RTN, OUT–RTN, D3 역전압 차동 측정 (전 온도) | 정격 이내, 손상 없음, 자동 복귀 |
| T2 | RS-485 서지: 결합망 42 Ω, ±1 kV 선–대지·선–선, 극성·횟수 명시 | 손상 없음, 통신 복귀, 오류율 |
| T3 | 출력: 12/24/28 V × 0/20/24 mA × 0/5/10 V, 부하·케이블 용량, 단락·오결선 해제 시 단자·DAC 측 파형 | 과도 한계·복귀 시간 사양 이내 |
| T4 | VAO 16.1 V (결정 #37): −40/25/85 °C, 12–28 V 입력, 기동·차단·부하 스텝 중 전압·리플, 12 V 드롭아웃 동작 | 15.5–16.6 V (≥ 18 V 입력), DAC AVDD ≥ 10 V |
| T5 | 두 출력 최대 부하 + RS-485 연속 송신 + 최대 연산, 12 V: 입력 전류·eFuse 여유, 몰딩 내부 온도 | 제한 미도달, 온도 사양 이내 |
| T6 | 외부 핀 쌍 ±30 V 매트릭스: 전원 OFF / 12 / 28 V × 출력 −30 / 0 / +30 V, 모드·채널별, 전류 제한·유지 시간 기록 | 손상 없음, 복귀 후 오차 사양 이내 |
| T7 | 센서: 온도·배선·몰딩·ESD 후 영점·스팬 변화, 센서 양단 파형 | 정확도 사양 이내 |

## 8. 재검수 때 넘길 자료

저장소 `okchois/Oilinwater` 브랜치 `claude/oil-moisture-transmitter-shji8x`: 회로도 원본(`hardware/kicad/HMT500(260313A)/`), 넷리스트 검사(`hardware/kicad/check_netlist.py`), PCB 배치, 부품리스트(LCSC), `docs/decision-log.md`, `docs/hw/final-review-260313A.md`, 이 문서.
