okchois/Oilinwater/docs/hw/final-review-260313A.md

# HMT500(260313A) 회로 확정 전 3중 검토 + RS-485 몰딩 후 펌웨어 업데이트 검토

작성 2026-09-30 · 대상: 회로도 v0.8 (`hardware/kicad/gen_hmt500.py`), PCB 배치 rev 3 (배선 전)

## 검토 방법

서로 독립된 검토 3회 + 부트로더 검토 1회. 각 검토는 넷을 하나씩 따라가며 제조사 데이터시트 원문과 대조했다.

| 검토 | 범위 | 대조한 원문 |
|---|---|---|
| 1 전원·보호 | M12 입력 → 보호(GDT·TVS·초크) → eFuse TPS26600 → 벅 LMR36006 → LDO → 각 IC 전원, 4–20 mA 출력단, 샤시·접지, 서지·역접속·오배선 | TI SLVSDG2G, SNVSB48C, SLVSFE3C, SBAS528D, SBVS338H, SLVSEG2B, OPA197 |
| 2 측정·MCU | PCAP04, ADS1220 Pt1000, STM32G0B1 핀·AF, SPI 모드, DAC SPI 게이트, RS-485, J1·J2·J3 핀 배정 | TI SLLSF20B, SBAS501D, SBAS528D, ScioSense PCAP04 DS-6, ST 공개 핀 데이터(GitHub XML) |
| 3 일치·제조성 | 심볼 핀 ↔ 풋프린트 패드 ↔ 데이터시트 패키지, 정격(전압·유전체·전력), 넷 무결성, 배치(발열·샤시 간격·배선 가능성) | 위 TI·ScioSense 원문 + KiCad 라이브러리 |
| 부트로더 | 몰딩 후 M12(전원 + RS-485)만으로 펌웨어 업데이트 가능 여부 | TI SLLSF20B, `docs/rs485-bootloader-design.md`, `firmware/bootloader/` |

공통: `check_netlist.py` 74 / 74 넷 일치, `tests.test_kicad_gen` 통과. 막힌 사이트: st.com, littelfuse.com, bourns.com, we-online.com, jst-mfg.com → 해당 값은 "확인 필요".

## 결론

**아직 확정하면 안 됩니다.** 모든 IC의 핀 번호·패드는 데이터시트와 일치하고 회로 구조도 맞지만, 서지·과전압 복귀·벅 입력 콘덴서 등 **몰딩 후에는 고칠 수 없는 항목**이 있습니다. 아래 A는 대부분 부품 1–2개 추가·값 변경으로 해결됩니다.

## A. 확정 전 반드시 고칠 것 (회로)

| # | 문제 | 근거 | 수정 | 검토 |
|---|---|---|---|---|
| A1 | **과전압 차단 후 복귀 안 됨** (U1 TPS26600, R3/R4/R5) | OVP 상승 29.0 V(27.99–30.45), 하강 26.8 V(25.96–27.97) (SLVSDG2G 7.5, 분압비 24.39). 26–28 V 전원에서 핫플러그 링잉·EFT로 한 번 차단되면 전원이 내려갈 때까지 꺼진 채 유지. 공차 하한 개체는 28 V 정상 전원에서도 차단. OVP를 올리면 U9/U10 +Vs(최대 32 V) 초과 | **결정 필요:** (a) 사양을 **12–26 V**로 (회로 변경 없음), 또는 (b) R5 36.5 k (상승 32.6 V / 하강 30.1 V) + U9/U10 +Vs를 VIN_P에서 100 Ω + 27 V 제너 + 100 nF로 분리 | 1 |
| A2 | **음(−) 서지 때 eFuse IN–OUT 역전압 초과** (U1, D2 SMBJ33CA) | IN–OUT 최소 −60 V (−70 V 10 ms). −1 kV 선간 서지에서 D2가 −45…−53 V로 잡는 동안 VIN_P는 +24…28 V(약 17 µF) → IN–OUT −69…−81 V | D2 → **TVS3301DRBR** (이미 BOM에 있음, ±33 V, 42.5 V 클램프) 또는 VIN_F→U1 IN 직렬 100 V 쇼트키(0.4 V 손실). A1과 함께 판단. 몰딩 전 서지 사전 시험 | 1 |
| A3 | eFuse 입력 콘덴서 부족 | SLVSDG2G 11.1: TVS 사용 시 입력 ≥ 1 µF, 12.1: IN 가까이. 현재 C1 100 nF, U1에서 25 mm | **U1 IN(1·2)–GND(9)에 1–2.2 µF 100 V X7R 1210 추가**, D2를 U1 옆으로 | 1 |
| A4 | **벅 LMR36006 입력 콘덴서 없음** (U2) | SNVSB48C 9.2.1.2.6·표 1: CIN 4.7 µF + 220 nF × 2를 "가능한 한 가깝게". 현재 VIN_P 콘덴서(C5, C7)는 U2에서 약 11 mm, 220 nF 없음 | **220 nF 100 V X7R 0603 × 2 (핀 2–1, 10–11) + 4.7 µF 50 V X7R를 U2 옆**. NC 핀 3 → BUCK_SW (데이터시트 권장) | 1·3 |
| A5 | **RS485_DE가 리셋·부팅 중 떠 있음** (U11 DE·/RE 묶음 ↔ PA1) | THVD24x0 표 5-1: DE 내부 2 MΩ 풀다운, /RE 2 MΩ 풀업 → 묶으면 VCC/2 부근(불확정). STM32 핀은 리셋 후 아날로그(부동) → 송신기가 켜져 버스를 막을 수 있음. 11.1항: enable 선 1–10 kΩ 풀업/풀다운 권장 | **RS485_DE – GND 10 kΩ 추가**. 부트로더에도 필수 | 2·부트 |
| A6 | 샤시 저항 R2 정격 (1 MΩ 0603, CHASSIS–GND) | GDT1과 병렬 → 서지 때 수백 V 임펄스. 0603 정격 약 75 V / 과부하 150 V, 패드 간격 0.8 mm | **1 kV 이상 고전압 칩 저항** (HV 1206/2010) 또는 2–3개 직렬 | 1·3 |
| A7 | X5R 콘덴서 (85 °C 한계) | C6, C10 (22 µF), C9, C12 (1 µF), C13, C24 (10 µF), C18, C25 (4.7 µF). 몰딩 + 자체 발열로 85 °C 초과 | **모두 X7R** (LMR36006도 X7R 요구). 1210 이상(C3, C5, C7, C43)은 소프트 터미네이션(에폭시 응력) | 1·3 |
| A8 | **DAC8760 발열** (U7/U8) | 28 V·24 mA 단락 최악 0.73 W/채널, 2채널 1.46 W. θJA 32 °C/W(JEDEC)로도 85 °C 주위에서 TJ ≥ 108 °C, 몰딩 튜브 안은 더 높음. 또 U8은 PCAP04 바로 아래, U7은 ADS1220 옆(보드 반대면) | **결정 필요:** BOOST NPN 자리(SBAS528D 8.4.2, 그림 8-6) DNP로 양 채널 추가 + DAC를 측정부에서 먼 뒤쪽으로 재배치. 몰딩 시제품 발열 시험 | 1·3 |
| A9 | SWD 핀 ERC 오류 (U4 35·36) | 생성기에서 35·36에 no-connect 표시가 붙은 채 J2와 연결됨 → KiCad 넷 이름 `unconnected-(J2-SWDIO)`. PCB 넷은 정상 | 생성기에서 nc 제외 + SWDIO/SWCLK 라벨, 검사기가 `unconnected-*` 다핀 넷을 오류로 | 3 |
| A10 | JST SH/GH 커넥터 −25 °C 정격 (J1, J3) | 부품표 기록 −25~+85 °C, 제품은 −40 °C | JST에 −40 °C 사용 확인 또는 −40 °C 정격 품목 (같은 핀 배정) | 3 |

## B. 확정 전 권장 (회로, 부품 0–2개)

| # | 내용 | 수정 | 검토 |
|---|---|---|---|
| B1 | SGOOD 입력: PC6/PC7이 PB6/PB7과 EXTI 6·7 충돌 + SGOOD High가 2.0–3.0 V라 STM32 VIH(≈2.31 V, 미확인) 경계 | OUT1/2_SGOOD → **PA0(11), PA4(15)** (두 검토가 같은 핀 제안, ADC로도 읽기 가능) | 1·2 |
| B2 | DAC LATCH 선 리셋 중 부동 | DAC1/2_LATCH 10 kΩ 풀업 → +3V3. (선택) CS_ADC·CS_CDC 100 kΩ 풀업 | 2 |
| B3 | RS-485 속도 등급 | THVD2450(50 Mbps) → **THVD2410DR**(500 kbps, 같은 핀) — Modbus 9.6–19.2 kbps, EMC·반사 유리 | 2 |
| B4 | R31/R41 10 k: ±30 V 오배선 때 93 mW, 무전원 때 VIN_P로 역급전 | **100 kΩ** (OPA197 바이어스 pA) | 1 |
| B5 | U12/U13 OPA197 V+ = VIN_P, DAC AVDD는 10 Ω 뒤 → +VSENSE가 AVDD보다 높아질 수 있음 | U12/U13 V+를 DAC1/2_AVDD로 (비용 0) | 1 |
| B6 | 국부 바이패스 부족 | U9/U10 +Vs 100 nF, U3 LDO 입력 1 µF | 1 |
| B7 | DC 바이어스 후 용량 부족 | PCAP04 VDD18 C25 → 10 µF, VDD33 → 22 µF (또는 10 µF × 2) U5 가까이 | 3 |
| B8 | ADS1220 입력 필터 | C27 10 nF **C0G** 명시, (선택) 공통 모드 1 nF C0G × 2 | 2 |
| B9 | 전원 전압 감시 없음 (UVLO 8 V ~ DAC 최소 10 V 사이 동작) | VIN_P 분압(100 k / 10 k) → 남는 ADC 핀 | 1 |
| B10 | 클럭: 크리스털 없음 (HSI16으로 Modbus, −40/+85 °C 여유 얇음) | HSE(PF0/PF1) 또는 32.768 kHz(PC14/PC15) 자리 DNP | 2·부트 |
| B11 | J3 센서선 ESD (PCAP04 HBM ±1 kV) | 저용량·저누설 ESD 어레이 자리 DNP | 2 |
| B12 | 센서 기준 C22 220 pF는 MK33-W mini(200 pF) 기준. MK33-W(300 pF) 채택이면 270–330 pF | 센서 품번 확정 후 값 결정 | 2 |
| B13 | 음(−) 출력 서지 때 TPS26611 IN–OUT 55 V 초과 가능 (에너지는 DAC 전류로 제한, TI 그림 9-14와 같은 구성) | 서지 사전 시험 항목. (선택) 저누설 클램프 자리 | 1 |

## C. 사양 정리 (문서)

- 입력 절대 최대 **33 V DC 연속** (TVS 때문). circuit-design.md의 "60 V까지 보호"·"60 V 1분 시험" 삭제 — 60 V에서는 D2·R1 파손.
- 전류 출력 부하: **12 V 전원에서 ≤ 350 Ω**, 500 Ω은 전원 ≥ 16 V (계산: 12 V에서 24 mA 최대 361 Ω).
- 문서 갱신: circuit-design.md(22 µH → 15 µH, GDT 품번, 최대 부하 전류 ≈ 90 mA, 옛 부품번호), R19 0.02 %(결정 기록의 0.01 % 정정), kicad README의 VERIFY/TBD.

## D. 배치 (배선 전, 배치 승인 전에 고칠 것)

| # | 내용 |
|---|---|
| D1 | J5 샤시 납땜 구멍이 U2(아랫면, 0.6 mm)·U3 +5V(1.3 mm)와 너무 가까움 → 손납땜 때 브리지 → 샤시 절연(GDT·R2) 무력화. **J5 둘레 양면 2–3 mm 동박 금지**, J5 또는 U2/U3 이동 |
| D2 | GDT1·C3·R2를 J5 옆(또는 입력 GND 노드)에 모으고, CHASSIS는 보드 가장자리로 짧고 넓게, 다른 넷과 2 mm 이상. 현재 GDT1 CHASSIS 패드가 R31(OPA197 입력)·U8·C40(DAC REF)과 0.8–0.9 mm |
| D3 | DAC8760 두 개를 측정부(PCAP04, ADS1220, C22, R19)에서 먼 뒤쪽으로 (A8) |
| D4 | 벅 부품(C8, C9, R8/R9/C11, 새 CIN) 핀에 바짝, MCU 디커플링 C14/C15/C20 핀에 바짝, C41을 D30 옆으로 |
| D5 | U1 방열 비아는 EF_RTN 전용 섬에만 (GND 면 금지), U5 EP 페이스트 ≤ 30 % |
| D6 | 풋프린트 라이브러리 이름을 프로젝트 라이브러리로, 누락된 넷 라벨 추가 (KiCad에서 "PCB 갱신" 때 넷 이름 유지) |

## E. 확인된 것 (문제 없음)

- **핀·패드:** STM32G0B1CCT3 LQFP48 전 핀과 AF(SPI1 AF0, SPI2 AF0, SPI3 AF9, USART2 TX/RX/DE AF1), PCAP04 QFN24, ADS1220 TSSOP16, DAC8760 PWP 24핀, TPS26600 PWP(패드 = RTN), LMR36006 RNX(자체 풋프린트 = TI 랜드 패턴), TPS7A20, TPS26611 DDF, OPA197, THVD2450, 74LVC2G32, TVS3301(패드 부동) — 모두 데이터시트와 일치. PCB 패드 넷 = 의도 넷.
- **측정:** PCAP04 플로팅 싱글 모드(PC0/PC1 기준 C22, PC2/PC3 센서, DC 없음), SPI 모드 1, VDD18/VDD33 최소값 충족. ADS1220 기준 250 µA × 4.02 k = 1.005 V(≥ 0.75 V), IDAC 순응 전압 여유, 게인 ≤ 2, SPI 모드 1 전용 버스.
- **출력:** DAC SPI 모드 3 + OR 게이트 SCLK 게이트(그림 8-9), SDO 3상태 35 ns, ALARM 10 k 풀업, DVDD 외부 3.3 V. TPS26611 방향·설정(32 mA 한계·자동 복귀). TVS3301 ±33 V·27 A.
- **전원:** eFuse UVLO 8.6 V / ILIM 149 mA / 돌입 98 mA, RTN 분리(9.3.5.5). 벅 5.02 V, 15 µH / 22 µF × 2 / 20 pF = 표 1. LDO 조건.
- **역접속 −30 V, 모든 핀 쌍 ±30 V 오배선:** 절대 최대 초과 없음 (R31/R41 전력만 B4).
- **RS-485:** 반이중 2선, 내장 페일세이프, 종단 없음(노드로 맞음). **M12 핀 배정 = EE364** (8 V+, 6 GND, 3 A, 2 B, 4/5 OUT).
- 부품번호 84개 중복 없음, 모든 넷 2패드 이상, IC 전원 핀 미연결 없음.

## F. RS-485 펌웨어 업데이트 (몰딩 후)

**가능 — 단, A5(DE 풀다운)와 아래 펌웨어 조건이 있어야 "벽돌 안 됨"을 보장.**

- **방식:** 플래시 앞 32 KB 자체 부트로더(`docs/rs485-bootloader-design.md`), USART2 PA2/PA3 + 하드웨어 DE(PA1 AF1). M12의 전원·RS-485만 사용 → 몰딩 후 BOOT0·NRST·SWD 불필요.
- **ST 내장(ROM) 부트로더는 사용 불가:** USART2를 보긴 하지만 DE(PA1)를 켜지 못해 응답 불가. 옵션 바이트는 nBOOT_SEL = 1, nBOOT0 = 1 유지.
- **벽돌이 안 되는 이유:** 부트로더 영역은 지우지 않고 쓰기 보호(WRP). 펌웨어 헤더를 **마지막에** 기록 → 정전·통신 끊김·손상 이미지면 헤더가 없어 다음 부팅에 부트로더에 머묾 → 다시 업데이트. 다른 하드웨어용 이미지는 하드웨어 ID로 거부. 교정·설정은 펌웨어 영역 밖.
- **추가해야 할 펌웨어 (CRC는 맞지만 멈추는 펌웨어 대비):**
  1. 전원 켠 뒤 약 1 초 복구 창 (고정 19200 8E1 + 저장 설정, 매직 요청에만 반응) — 전원이 M12에 있으므로 전원 재투입으로 항상 진입
  2. 부팅 확인 카운터 (백업 레지스터, 3회 미확인 또는 IWDG 리셋 반복 → 부트로더 유지)
  3. 하드웨어 워치독 리셋부터 동작 (IWDG_SW = 0), 페이지 지우는 사이 갱신
- **옵션 바이트:** RDP 레벨 1 (IAP 가능), 레벨 2 금지. WRP 0–15쪽. BOR 높은 문턱.
- **업데이트 중 4–20 mA:** 들어가기 전 NAMUR 고장 전류(≤ 3.6 mA) 또는 마지막 값 유지(설정). 부트로더에도 DAC 최소 드라이버.
- **남는 위험:** 단일 슬롯(업데이트 끝날 때까지 측정 없음), 업데이트 중 버스 점유(19200 bps에서 약 76 s), 부트로더 자체 버그(몰딩 전에 충분히 검증, 현장에서 부트로더는 갱신하지 않음).

## G. 확인하지 못한 것

- ST 원문(st.com 막힘): HSI16 온도 정확도, USART 수신 허용 오차, VIH, DUAL_BANK·BOOT_LOCK 동작, 에라타 ES0548.
- Littelfuse·Bourns·Würth(막힘): SMBJ33CA/SMDJ36CA 서지 전류, GDT 방전 개시·홀드오버, 초크 DCR·권선 방향, R1 펄스 정격, L2 Isat.
- HTX99R 핀 배정, 센서 프로브 절연 내압(라인–접지 서지가 센서선으로 가는지).
- 몰딩 상태 열저항(시제품 측정 필요), 서지 전류 분배(시뮬레이션 또는 사전 시험), IEC 61326-1 DC 포트 라인–접지 시험 등급(1 kV 또는 2 kV).

## H. 반영 결과 — 회로도 v0.9 · 배치 rev 4 (2026-09-30, 결정 #32)

두텍 결정: 전원 12–28 V 유지, DAC 발열 = 자리 추가 + 재배치, A·B 전부 반영, 펌웨어 업데이트 = 자체 부트로더(결정 #31).

| 항목 | 결과 |
|---|---|
| A1 과전압 복귀 | ✅ R5 36.5 k → OVP 32.6 V / 복귀 30.1 V. TPS26611 +Vs = VS_CLAMP **이미터 폴로워** (Q1 MMBTA06, 베이스 R50 10 k + D50 BZX84C27 → +Vs ≈ 26.3 V 이하, 정상 24 V에서 약 0.7 V 강하, C53 + 핀마다 C46/C56). 재검토에서 첫 안(R50 1 k 직렬)은 +Vs 전류로 2–3.5 V가 떨어져 바꿈 |
| A2 음(−) 서지 | ✅ D2 → TVS3301DRBR, U1 옆 (0.2 mm). 여유는 eFuse IN–OUT 펄스 정격 −70 V / 10 ms 기준. **입력 DC 절대 최대 33 V** (TVS3301이 DC 약 34.5 V 이상에서 손상) |
| A3 eFuse 입력 C | ✅ C2 2.2 µF 100 V X7R, U1 옆 (0.35 mm) |
| A4 벅 입력 C | ✅ C16/C17 220 nF 100 V (U2 핀 0.3 mm), 벌크 = C5 10 µF를 U2 옆으로 (별도 C19는 자리 부족으로 빼고 C5가 겸함), U2 핀 3 = BUCK_SW |
| A5 DE 풀다운 | ✅ R60 10 k |
| A6 R2 | ✅ 1 MΩ 고전압 1206 (품번 확인 필요) |
| A7 X5R | ✅ 전부 X7R (일부 품번 확인 필요) |
| A8 DAC 발열 | ⚠️ DAC를 측정부에서 떼어 x 42–48로 재배치. **부스트 자리는 넣지 못함** — DAC 옆에 두면 ISET-R·REF C·AVDD 부품이 10–20 mm 밀려남. 몰딩 시제품 발열 시험으로 판단 |
| A9 SWD ERC | ✅ no-connect 제거, 검사기가 `unconnected-*` 다핀 넷을 오류로 |
| A10 JST −40 °C | ⏳ JST 확인 대기 (미결) |
| B1 SGOOD | ✅ PA0/PA4 (EXTI 0·4, ADC 가능). CS_CDC는 PA15로, PB0은 VIN_SENSE |
| B2 풀업 | ✅ R10/R11 10 k (LATCH), R12/R13 100 k (CS) |
| B3 THVD2410 | ✅ |
| B4 R31/R41 | ✅ 100 k |
| B5 OPA197 V+ | ✅ DACn_AVDD, C45/C55 |
| B6 국부 C | ✅ C46/C56 (+Vs), C26 (LDO 입력) |
| B7 PCAP04 C | ✅ C25 10 µF, C24 22 µF 10 V (1206 X7R) |
| B8 C27 | ✅ 10 nF C0G (공통 모드 C는 선택 — 넣지 않음) |
| B9 전원 감시 | ✅ R14/R15/C30 → PB0 |
| B10 크리스털 | ⚠️ 넣지 못함 (MCU OSC 핀 옆 자리 없음) → HSI 공장 트림 + 펌웨어 보정 |
| B11 센서선 ESD | ⚠️ 넣지 못함 (J3 옆 자리 없음) → 프로브 ESD 시험 후 |
| B12 C22 | ✅ 센서 MK33-W (300 pF) 확정(결정 #33) → C22 330 pF C0G 1% |
| D1 J5 | ✅ 가장자리 쪽(y 7.4)으로, 구멍 중심 ~ 코트야드 3.3 mm 양면 금지 (재검토: 2.5 mm는 코트야드 간격 1.15 mm뿐이라 늘림) |
| D2 샤시 부품 | ⚠️ CHASSIS 넷클래스 간격 1.0 mm(몰딩 안)·선폭 0.5, 부품 간격 +0.5 mm. 재검토 후 GDT1·C3·R2를 입력 보호부(U1·D2) 쪽 앞 구역으로 모음 → MCU·DAC·OPA197과 떨어짐. J5 패드까지 11–17 mm (J5 둘레 금지 구역 때문에 더 붙일 수 없음) → 배선 때 CHASSIS 전용 굵은 선 |
| D3 DAC 위치 | ✅ 측정부에서 약 5 mm 이상 |
| D4 핀 옆 부품 | ✅ 배치기에 **핀 지정 배치**("pin", IC, 핀번호) 추가. 패드 중심 거리: 벅 C16/C17 1.7–2.5 mm, DAC ISET R32/R42 1.7, REF C40/C50 2.1–2.2, DAC +3V3 C44 2.2, TPS26611 +Vs C46/C56 2.1–2.5, MCU C14/C20/C15 = U4 핀 4–6 바로 아래 아랫면 0.8–2.9 (윗면은 J3 하네스 통로). ⚠️ 남은 것: 벅 BOOT C8 5.4·VCC C9 6.2 mm (J5 금지 구역·U1 사이), U8 +3V3 C54 7.8 mm (핀 2가 가장자리 D1 옆) — 배선 때 짧은 전용 선 |
| D5 RTN 섬·EP 페이스트 | ⏳ 배선 때 |
| D6 라이브러리·라벨 | ⏳ 배선 전 정리 |

검증 (재검토 반영 후): 넷리스트 77/77 일치, 테스트 32개 통과, 조립 시뮬레이션 23항목 NG 0, 부품 84 → 102 (전부 배치, 윗면 38 / 아랫면 64).
