okchois/Oilinwater/docs/hw/humidity-sensor-selection.md

# 습도 센서 선정 — IST AG 정전용량식

작성일: 2026-09-29 · 대상: HMT500 오일 수분 (aw) 측정 · 자료: IST 제품 페이지·데이터시트 요약 (검색 결과. ist-ag.com은 이 환경에서 직접 열리지 않음)

## 1. 요구 조건

| 항목 | HMT500 요구 | 근거 |
|---|---|---|
| 측정 범위 | 0–100 % RH (aw 0–1) | 오일 포화 근처까지 |
| 오일 온도 | −40 ~ **+120 °C** | 설계 목표 (EE364: 80 °C / 옵션 100 °C) |
| 내화학성 | 광유·합성유·에스테르유, 첨가제 | 오일 속 상시 침지 |
| 크기 | 보호캡 Ø9 센서실, 캐리어 폭 4.5 mm 안 | 기구 Rev C (캐리어 9.5 × 4.5) |
| 측정 회로 | PCAP04 (정전용량), 기준 C 220 pF C0G | 회로도 v0.3 |
| 접속 | 4핀 (HTX99R 커넥터 검토 중, 2.54 격자) | 결정 #11 |

## 2. 후보 비교

| 제품 | 용량 (30 % RH, 23 °C) | 온도 범위 | 최대 이슬점 | 크기 | 특징 | 오일 적합성 |
|---|---|---|---|---|---|---|
| **MK33-W mini** | 200 pF ± 40 | **−40 ~ +190 °C** | +95 °C | **5.0 × 3.81 × 0.4/1.2 mm**, 선 10 mm | 응답 t63 < 6 s, 히스테리시스 < 2 % RH | **IST가 오일용으로 권장.** 고온·내화학성 |
| MK33-W | 300 pF ± 40 | −40 ~ +190 °C | +95 °C | 10.8 × 3.81 mm, 선 10 mm | 감도 0.45 pF/% RH, 직선성 < 2 % RH, 측정 주파수 1–100 kHz (권장 10 kHz) | 오일용 권장. 캐리어(9.5 mm)보다 김 |
| P14 Rapid-W | 140 pF ± 40 | −80 ~ +150 °C | +85 °C | 소형 | 빠른 응답, 기상용 (라디오존데) | 온도는 되지만 오일 내화학성 언급 없음 |
| P14-W / P14 Classic | (P14 계열) | 약 −40 ~ +150 °C (확인) | — | 소형 | 범용 | 범용. 오일 전용 아님 |
| HYT 271 (MK33 탑재형) | 디지털 I²C, 공장 교정 | 모듈 −40 ~ +125 °C (확인) | — | 모듈 | ±1.8 % RH, ±0.2 °C. IST 오일 평가키트에 사용 | 센서는 MK33. 모듈 전자부 때문에 125 °C 한계 |
| HYT 939 | 디지털 I²C | −40 ~ +125 °C | — | TO 캔 | ±1.8 % RH, ±0.2 °C | 공기용. 오일 침지 비권장 |

## 3. 선정

### 1순위: **MK33-W mini (200 pF)**

- **오일용 센서입니다.** IST가 MK33을 오일 측정용으로 권장하고, 190 °C까지 쓸 수 있으며 내화학성이 가장 좋습니다. 120 °C 목표에 충분한 여유가 있습니다.
- **크기가 맞습니다.** 5.0 × 3.81 mm라서 캐리어(9.5 × 4.5)에 Pt1000과 함께 올라갑니다. 일반 MK33-W(10.8 mm)는 캐리어보다 깁니다.
- **회로를 바꿀 필요가 없습니다.** 기준 커패시터 220 pF C0G가 센서 용량(200 pF)과 비슷해서 PCAP04 비율 측정에 맞습니다.
- 두텍이 이미 공급받는 "IST MK 센서"와 같은 계열입니다. 공급 품번이 MK33-W mini인지 확인해 주세요.

### 대안: **HYT 271 MK33 (디지털 모듈)**

- 공장 교정된 I²C 출력이라 PCAP04, ADS1220, Pt1000, 기준소자가 빠집니다. 전자부 원가가 약 $10~14 줄고 교정 공정도 단순해집니다.
- 신호가 4선(VDD, GND, SDA, SCL)이라 **HTX99R 4핀 커넥터와 그대로 맞습니다.**
- 대신 모듈 전자부의 최고 온도가 약 125 °C라 120 °C 운전에는 여유가 거의 없습니다. 정확도(±1.8 % RH)도 EE364 수준에 겨우 맞습니다.
- → 오일 최고 온도를 100 °C 이하로 정하면 원가 절감안으로 검토할 가치가 있습니다.

## 4. 설계 반영 사항

| 항목 | 내용 |
|---|---|
| PCAP04 기준 C | 220 pF C0G ±1 % 유지 (MK33-W mini 200 pF). 일반 MK33-W(300 pF)로 바꾸면 270~330 pF로 변경 |
| 측정 방식 | PCAP04 방전시간 측정. IST 권장 교류 주파수(1–100 kHz)와 방식이 다르므로 초기 시험에서 누설·분극 영향 확인 |
| 커넥터 핀 배정 (HTX99R 4핀) | 습도 2핀 + Pt1000 2핀 → **Pt1000이 2선식이 됨** (현재 회로는 4선식). 리드 저항 오차 보정 필요 또는 핀 수 재검토 |
| 교정 | aw 기준점(포화염 또는 습도발생기) + 오일 온도 보상. 공급 로트별 C30 편차(±40 pF)는 1점 교정으로 제거 |

## 4A. 원문 스터디 후 추가 (2026-09-29)

두텍이 제공한 데이터시트·응용노트·백서로 확인한 내용은 [IST MK33 스터디](../reference/ist-mk33-study.md)에 정리했습니다. 핵심은 네 가지입니다.
- **MK33-W mini의 주문 코드는 150138**입니다(백서).
- **최대 이슬점이 95 °C**입니다. 그래서 120 °C에서는 aw 0.43까지만 측정할 수 있고, 사양서에 이 한계를 적어야 합니다.
- **DC 바이어스 없는 교류(1–100 kHz)로 측정**해야 합니다. PCAP04 구동 방식이 이 조건을 만족하는지 확인해야 합니다.
- **온도 보정은 필수**입니다. 보정하지 않으면 100 °C에서 10 % RH 이상 틀어집니다. 교정은 납땜 후 5일이 지난 뒤에 합니다.

## 5. 확인 요청

1. 현재 공급받는 IST MK 센서의 정확한 품번 (MK33-W / MK33-W mini / 기타)
2. 오일 최고 온도 목표 (120 °C 유지 여부) — HYT 271 모듈안 판단용
3. HTX99R 커넥터 4핀 배정 — Pt1000 2선식 허용 여부

## 참고 자료

- MK33-W: https://www.ist-ag.com/en/products/capacitive-humidity-sensor-mk33-w
- MK33-W mini: https://www.ist-ag.com/en/products/capacitive-humidity-sensor-mk33-w-mini-200pf-40-pf
- MK33-W 데이터시트: https://www.ist-ag.com/sites/default/files/downloads/DHMK33-W_E.pdf
- P14 Rapid-W: https://www.ist-ag.com/en/products/capacitive-humidity-sensor-p14-rapid-w-140pf-40-pf
- Moisture in oil Eval Kit (HYT271 MK33): https://www.ist-ag.com/en/products/moisture-oil-eval-kit
- HYT 939: https://www.rapidonline.com/ist-ag-hyt-939-digital-humidity-temperature-sensor-50-9443
