okchois/Oilinwater/docs/reference/ee364-summary.md

# E+E EE364 원문 확인 요약 (구조 참고 제품)

출처: 사용자 제공 PDF — **Datasheet EE364 v1.13 (07-2026)**, **Quick Guide EE364 v3.7 (08-2025)**. 원본 PDF는 저작권 문제로 저장소에 넣지 않았습니다.

> EE364는 구조 참고용 E+E 상용 제품이며 두텍 제품이 아닙니다.

## 1. 치수 (G½ ISO형, mm)

| 항목 | 값 | 해석 |
|---|---|---|
| 전장 | **140** | 프로브 끝 ~ 커넥터 끝 |
| 노출 프로브 | **34** | 프로브 끝 ~ 나사 시작 (필터캡 Ø12) |
| 나사 | G½ | 길이 = 140 − 92 − 34 = **14** |
| 씰면 ~ 커넥터 끝 | **92** | |
| 씰면 ~ 하우징 끝 | **77** | 커넥터 돌출 약 15 |
| 육각 | **AF27** | 씰면 바로 뒤 |
| 하우징 외경 | **Ø30** | 도면상 단차가 있는 원통 (앞쪽 Ø30 → 가운데 조금 가는 부분 → 끝단 칼라) |
| 프로브 외경 | **Ø12** | 측면 구멍 2열 × 4개 |
| NPT형 | ½" NPT, AF22, 노출 51, 나사면 뒤 89 (하우징 끝까지 74) | |

## 2. 사양

| 항목 | EE364 |
|---|---|
| 측정량 | aw, 수분 함량 x [ppm], T |
| aw 정확도 (20 °C) | ±0.02 aw (0–0.9), ±0.03 aw (0.9–1). k=2 불확도 포함 |
| ppm 범위 | 0–100 000 ppm (오일 의존), ppm 출력은 0–100 °C에서 유효 |
| 온도 정확도 | ±0.2 °C (20 °C, 오일 중), 분해능 0.01 °C |
| 응답시간 | 오일 점도와 유속에 크게 의존 (사용자 매뉴얼 그래프) |
| 오일 온도 | −40~+80 °C / 옵션 HM2 −40~+100 °C |
| 주위 온도 | −40~+60 °C / −40~+80 °C |
| 압력 | **0–20 bar** |
| 재질 | 하우징·필터캡 SUS 1.4404 (316L) |
| 보호 등급 | **IP65** / NEMA 4X |
| 아날로그 출력 | 4–20 mA × 2, **3선식**, RL < 500 Ω, 분해능 2 µA, 측정값·스케일 자유 설정 |
| 디지털 | RS-485 (1 unit load), Modbus RTU, FLOAT32 |
| 전원 | **10*–28 V DC** (*최소 = 10 V + 0.02 × RL), Class III |
| 소비전류 | < 20 mA + 부하 전류 |
| 커넥터 | M12×1 8핀 |
| EMC | EN (IEC) 61326-1, 61326-2-3 산업 환경, FCC Part 15 Class B |
| 증명서 | DIN EN 10204-3.1 검사 성적서 기본. ISO 17025 교정 성적서 옵션 |
| 설정 | PCS10 무료 소프트웨어 + Modbus 설정 어댑터(M12↔USB, HA011013) |

### 주문 옵션

- 공정 연결: G½ ISO(PA1) / ½" NPT(PA2)
- 센서 보호: LeadsShield(C2, 리드 보호), ChemShield(C4, 오일 열화·에스테르유 대응 코팅), 둘 다(C6)
- 필터: 유속 < 1 m/s용(F13) / > 1 m/s용(F18)
- 출력 1·2 측정값과 스케일: 기본값 OUT1 aw 0–1, OUT2 T −20~80 °C
- 단위: SI / US
- ppm 환산 오일 파라미터: 광유 변압기유 기본. 고객 오일은 **오일 2 L를 보내 E+E가 파라미터를 측정**(Oil-ppmcal)하거나, 포화곡선으로 계산(Oil-calc)
- 액세서리: 8핀 M12 소켓, 차폐 케이블(1.5/5/10 m), 샘플링 셀(PN40, DN25)

## 3. 핀 배치 (Quick Guide 원문 확인)

**EE364 표준 (M12 8핀)**

| 핀 | 신호 |
|---|---|
| 8 | 전원 V+ (10–28 V DC) |
| 6 | GND |
| 4 | 출력 1 (4–20 mA) |
| 5 | 출력 2 (4–20 mA) |
| 3 | RS485 A |
| 2 | RS485 B |
| 1, 7 | 결선도에 없음 (미사용) |

**EE364 OEM Style (RS485 전용, M12 5핀)**

| 핀 | 신호 |
|---|---|
| 1 | V+ |
| 3 | GND |
| 4 | RS485 A |
| 5 | RS485 B |

- 차폐 케이블 사용이 EMC 조건입니다.
- Quick Guide에는 선색이 나오지 않습니다(이전 문서의 선색은 검색 인용이었으며 표준 M12 케이블 색 기준).

## 4. Modbus (Quick Guide)

| 항목 | 값 |
|---|---|
| 공장 설정 | **9600 bps, 8E1, 주소 243** |
| 선택 가능 | 9600 / 19200 / 38400 / 57600 / 76800 bps, 패리티 N/O/E, 정지비트 1/2, 주소 1–247 |
| 통신 설정 레지스터 | 주소 0x00 (Modbus 주소), 0x01 (통신 설정) — FC06 쓰기 |
| 정보 | 시리얼 번호 ASCII 레지스터 1–8, 펌웨어 버전 레지스터 9, 센서 이름 레지스터 10 |

**측정값 (FLOAT32, FC03/FC04 읽기)**

| 측정값 | 레지스터 번호 (1부터) | 주소 (0부터) |
|---|---|---|
| 온도 T | 26 | 0x19 |
| 수분 활동도 aw | 52 | 0x33 |
| 수분 함량 x [ppm] | 54 | 0x35 |
| 오일 파라미터 A, B, C, D, E | 224, 226, 228, 230, 232 | 0xDF, 0xE1, 0xE3, 0xE5, 0xE7 |

- 오일 파라미터 쓰기(FC16):
  - 구형 방식: A, B만 주소 0x64, 0x66에 씁니다. 이때 C, D, E는 0으로 설정됩니다.
  - 펌웨어 2.0.22 이상: A–E를 0xDF부터 씁니다.
- **FLOAT32 워드 순서는 하위 워드 먼저(CDAB)입니다.** 문서 예시로 확인했습니다.
  - A = −100 → `00 00 C2 C8`
  - B = 7.3705 → `DB 23 40 EB`
- ppm 환산은 5개 파라미터 모델(A–E)입니다. 식 자체는 공개되지 않았습니다(AN0103 확인 필요).

## 5. 우리 설계에 주는 시사점

| 항목 | 반영 |
|---|---|
| 핀맵 | 우리 8핀 안(2: B, 3: A, 4: OUT1, 5: OUT2, 6: GND, 8: V+)이 **EE364와 일치함을 원문으로 확인**. 1, 7번은 EE364에서 미사용이므로 7번 AGND 제안과 충돌하지 않음 |
| 전원 | EE364는 10–28 V. 우리 안은 15–30 V(전압 출력 0–10 V와 전류 출력 부하 때문). 교체 호환을 위해 **최소 전압을 12 V 수준으로 낮출 수 있는지** 검토 (저전압 시 부하 저항 제한) |
| 사양 우위 | 압력 20 → 50/200 bar, 오일 100 → 120 °C, IP65 → IP67, 출력 전류 → 전압/전류 선택, RS-485 펌웨어 업데이트 |
| 정확도 | EE364와 같은 수준(±0.02/±0.03 aw, T ±0.2 °C)이 최소 목표 |
| 교체 호환 모드 | EE364 레지스터(0x19, 0x33, 0x35, 0xDF~), **CDAB 워드 순서**, 공장값 9600 8E1 주소 243을 재현하는 모드. 단, EE364는 주소 0x00이 "Modbus 주소" 레지스터라서, 우리 앱의 0x0000(모드 ID "AP")과 충돌함 → 호환 모드에서는 모드 ID를 다른 주소(예: 0xFF00)로 옮겨야 함. 부트로더·업데이트 도구도 함께 수정 필요 |
| 센서 보호 | ChemShield/LeadsShield에 해당하는 소자 보호 코팅을 IST AG에 문의 (에스테르유·해수 오염 대응) |
| 필터 | 유속별 필터캡 2종(< 1 m/s, > 1 m/s) → 우리 교체형 보호캡으로 대응 |
| 서비스 | 오일 파라미터 측정 서비스(오일 2 L 접수)는 우리도 교정실에서 제공 가능한 사업 요소 |
| 설정 도구 | PC 설정 SW + M 커넥터↔USB(RS-485) 어댑터 → 우리 `fwupdate.py`를 설정·업데이트 통합 도구로 확장 |
