okchois/Oilinwater/hardware/mech/out/HTX99R-SC_sensor_connector.pdf

## 정면도

3 5.5 1.5 1 1.5 5.5

7

15

18

3

### M10×1.0 (바디 체결)

### M10×1.0 (필터 캡)

Ø11

7 (맞변)

홈 Ø8.2 × 1.5

홈 Ø8.1 × 1.5

### C0.5 (양 끝)

## 단면 A-A

7.9

7

2.54

Ø7

### 4× Ø1.5 깊이 7.9, 입구 C0.2

### 4× □0.64 핀, 끝 C0.2

### 오목부 Ø7 깊이 7

## 윗면도 (센서 소켓 쪽)

2.54

2.5

A 4

A

## 아랫면도 (PCB 핀 쪽)

2.54

## 등각도 (참고, 2.5:1)

## 주기 (NOTES)

1. 형상·치수는 두텍 SolidWorks 모델 (HTX99R) Sensor Probe_Sensor Connector.STEP 에서 추출. 단위 mm.
2. 재질·공차·표면처리는 STEP에 없음 — 원 도면 또는 공급사 사양 확인. 일반공차 ISO 2768-mK 가정.
3. Ø10 두 곳은 나사, 위·아래 모두 M10×1.0 (두텍 확인 2026-09-30): 아래 = 바디 체결, 위 = 필터 캡 체결. 윗면 소켓 4× Ø1.5.
4. PCB 풋프린트 제안: 2×2, 피치 2.54, 도금 구멍 Ø1.0, 패드 Ø1.7. 핀 돌출 3.0 → PCB 1.6 t 관통 후 1.4.
5. 홈 Ø8.2 (플랜지 아래): O링 자리 (HMT500은 O링 8×1.2, Ø10 H8 밀봉면). 홈 Ø8.1 (플랜지 위): 위 나사 언더컷.
6. HMT500 Rev F 적용: 바디 앞 M10×1.0-6H 암나사에 체결, 필터 캡을 위 나사에 체결. 아랫면 핀 4× □0.64: 하네스 W-1 납땜 + 수축튜브 (포팅 없음)

# HTX99R-SC 센서 커넥터 — 정면도 · 단면 A-A · 윗면도 · 아랫면도 (5:1, 제1각법)

1 | 2 | 3 | 4 | 5 | 6 | 7 | 8

A

B

C

D

E

F

(주)두텍 DOTECH Co., Ltd. | HMT500(260313) 오일 수분 트랜스미터

품명 센서 커넥터 (HTX99R 센서 프로브)

도번 HTX99R-SC | Rev / 일자 A / 2026-09-29

재질 STEP에 재질 정보 없음 (확인)

척도 5 : 1 | 단위 / 투상 mm / 제1각법

일반공차 ISO 2768-mK

표면(지정 외) Ra 1.6 | 쪽 1/1

작성

### HMT500 설계

검토 | 승인
