okchois/Oilinwater/hardware/mech/out/m12/HMT500_M12_외형도_RevB.pdf

# HMT500 M12 8핀 커넥터 외형도

HMT500-P-204 / Rev B / 2026-10-02 / 기구 Rev I 기준

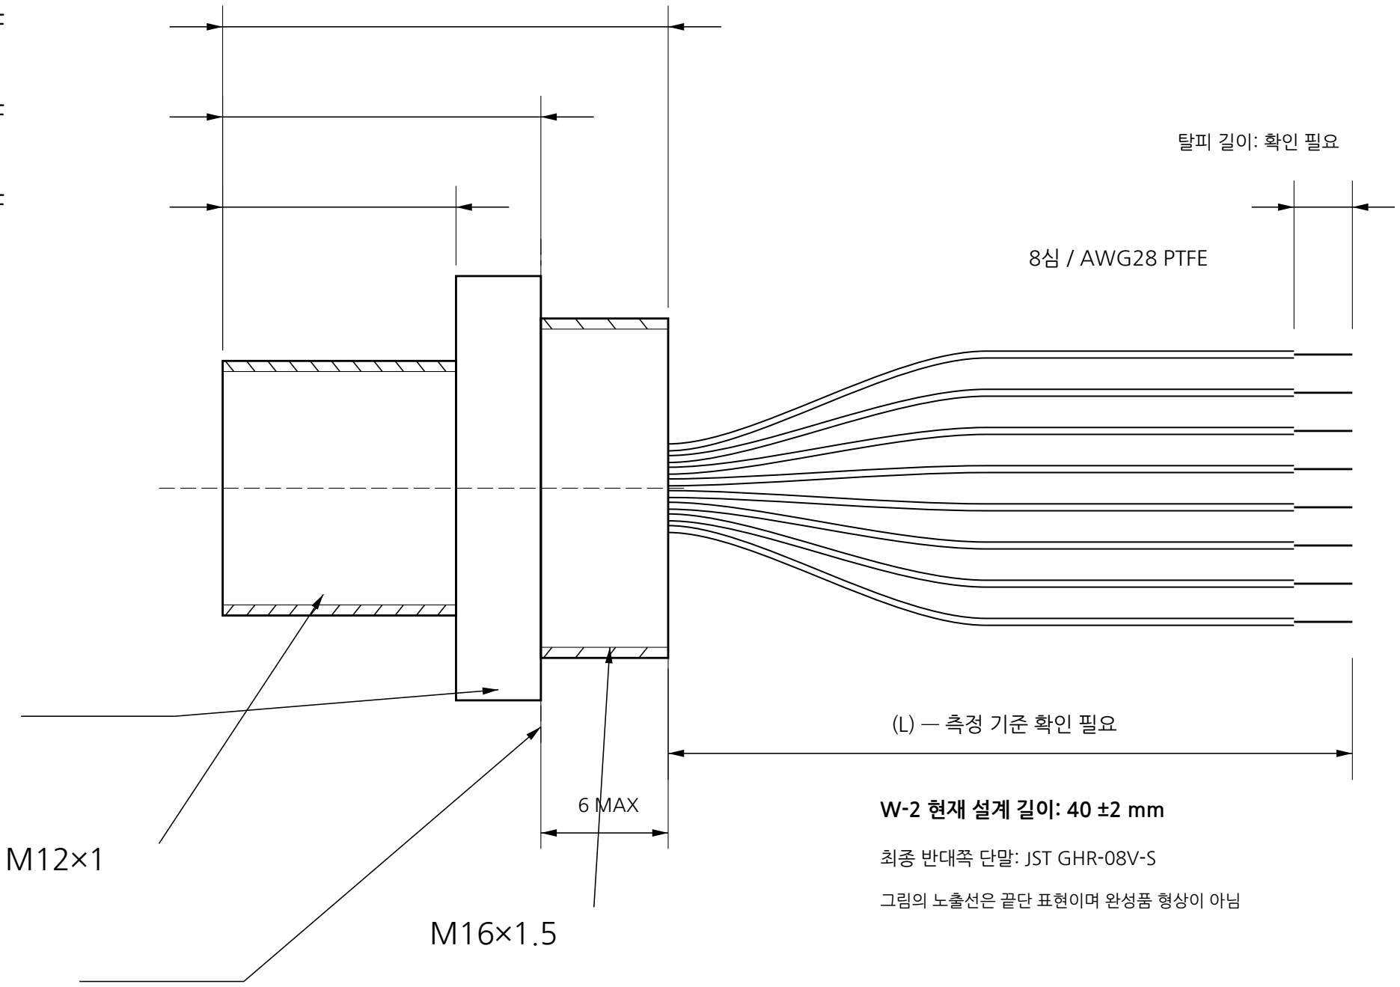
[picture p17: figure]
8심 / AWG28 PTFE; 최종 반대쪽 단말: JST GHR-08V-S; 그림의 노출선은 끝단 표현이며 완성품 형상이 아님; 6 MAX

## 21 REF

## 15 REF

## 11 REF

## Ø20 이하

A: 장착 기준면

### 안쪽 나사부 6 이하

주기: REF는 현 모델 참고치수. 실제 공급사 외형·가스켓·공구 맞변·핀 방향은 품번 확정 후 반영.

A-coded / 8핀 / Male. TURCK 참고 제품의 4핀 T코딩·25.8 mm·탈피 7 mm 치수는 적용하지 않음.

단위 mm / NTS / 선정 검토용 — 제조 승인 아님 | HMT500-P-204-OD / B
