okchois/Oilinwater/hardware/mech/out/m12/HMT500_M12_외형도포함_선정사양서_RevA.pdf

# M12 8핀 커넥터 — 외형·장착 조건

HMT500-P-204 | Rev A | 2026-10-02 | 기구 Rev I / PCB A5-R1
선정·견적 검토용 / 구매품 품번 미확정 / 단위 mm / 축척 없음 (NTS) | 1 / 2

접속부 M12×1과 장착부 M16×1.5는 서로 다른 나사입니다.

장치 내부 | 장치 외부 / 상대 케이블 접속
장착 수나사: M16×1.5 | 접속 수나사: M12×1

형식: A-coded / 8핀 / Male

어깨 외경: Ø20 이하

표현된 외형은 현 기구 모델입니다.

표준이 커넥터 몸체 전체 치수를

정하는 것은 아닙니다.

6 이하 | 4* | 11*

외부 돌출 15*

기준면 A: 엔드캡 뒤 끝면 x=77

* 4 / 11 / 15는 현재 모델 치수이며 선정품 실측값·표준 치수가 아닙니다.

장착 암나사 | 엔드캡 M16×1.5-6H, 모델 x71–77 (길이 6). 구매품 체결·씰 형상 대조 필요.
내부 여유 | PCB 뒤끝 x69 → 모델 커넥터 안쪽 끝 x71: 축 방향 2 mm. 납땜 핀·수축튜브 돌출은 별도.
공구 공간 | 어깨 Ø20 조건에서 M3 경사 주입 공구 여유 0.625 mm. 어깨 확대 시 재검사.
밀봉·고정 | O링/가스켓 형상, 장착 토크, 회전 방지, 체결 유효 길이: 선정품 도면으로 확인 필요.
선정 자료 | 공급사 2D 치수도·STEP·단자 방향도 요청. 안쪽 단자 전체 형상과 외부 돌출 길이를 포함할 것.

# M12 8핀 커넥터 — 전기·하네스·구매 사양

HMT500-P-204 | Rev A | 2026-10-02 | 기구 Rev I / PCB A5-R1
선정·견적 검토용 / 구매품 품번 미확정 / 단위 mm / 축척 없음 (NTS) | 2 / 2

### HMT500 핀 배정 (표준 공통 기능 배정이 아닌 본 제품 배정)

1 | 예비 / PCB NC | → J1.1
2 | RS485_B_EXT | → J1.2
3 | RS485_A_EXT | → J1.3
4 | OUT1_EXT | → J1.4
5 | OUT2_EXT | → J1.5
6 | GND_IN / 전원 | → J1.6
7 | 예비 / PCB NC | → J1.7
8 | VIN_EXT / 전원 + | → J1.8

### 선정 조건 및 현재 상태

접속 형식 | M12 A-coded, 8핀 수형, 직선, 전면 장착
장착 나사 | M16×1.5 (PG9·M16×1 등과 혼용 불가)
제품 사용 전압 | 12–28 V DC / 최대 28 V
커넥터 정격 | 30 V DC 이상 적용 여부 확인; 아래 참고품은 30 V
허용 전류 | 선정품·접점별·배선 규격으로 확인 필요
방수·온도 | 제품 요구와 체결 조건 확정 후 검증; 현재 보증 등급 미확정
하네스 W-2 | 8심 AWG28 PTFE, 현재 40±2 mm, JST GHR-08V-S
단자·배선 | 납땜형 또는 지정 리드선형. 실제 길이·피복·핀별 선색 확인
공통 주의 | 1·7번은 8심에 포함, PCB NC. 샤시는 별도 W-3 연결

핀 배열의 정면/배선면 방향·키 위치는 선정품 제조사 도면을 따릅니다. 본 표를 물리적 핀 위치도로 사용하지 마십시오.

제조사 공식 참고품 — 채택품 또는 무수정 호환품으로 승인한 것은 아닙니다.

[1] Phoenix Contact 1436424 · SACC-E-M12MS-8CON-M16/0,5 P

8핀 Male / A-coded / M16×1.5 전면 장착 / 30 V AC·DC / 2 A / 0.25 mm² 리드선 0.5 m.

현재 W-2의 AWG28·40 mm와 다릅니다. 외형·씰·내부 돌출·JST 압착 적합성을 별도로 확인해야 합니다.

제조사 제품 페이지 및 외형도 열기 [1] (https://www.phoenixcontact.com/en-fr/products/device-connector-front-mounting-sacc-e-m12ms-8con-m16-05-p-1436424)

[2] binder 76 0831 0011 00008-0200 · M12-A series 763

8핀 Male / M16×1.5 / 30 V / 2 A (UL 1.5 A) / 리드선 AWG24·0.2 m. 현재 W-2와 배선 규격이 다름.

제조사 제품 페이지·외형도·접속면 핀 배열 열기 [2] (https://www.binder-usa.com/us-en/products/automation-technology/m12-a/76-0831-0011-00008-0200-m12-a-male-panel-mount-connector-8-unshielded-single-wires-ip68-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)

발행 근거: hmt500_params.py / PCB J1 연결 정보 / 제조사 공식 페이지(2026-10-02 확인). 실제 M Connect 품번: 확인 필요.
