okchois/Oilinwater/hardware/mech/out/harness/HMT500_W-1_RevA.pdf

# HMT500 | W-1 센서 하네스

제작 검토용 · Rev A · 기구 Rev I / PCB A5-R1 기준 · 2026-10-02

### 길이 기준·탈피·압착 조건 미확정 — 양산 제작 승인 도면 아님

## 전기 연결 개략도 (핀 배열도 아님 / 축척 없음)

HTX99R-SC 뒤 납땜 핀 | JST SHR-04V-S → PCB J3
1 | SENS_C1 / MK33 전극 1 | 1
2 | SENS_C2 / MK33 전극 2 | 2
3 | PT_P / Pt1000 | 3
4 | PT_N / Pt1000 | 4

### 배선 사양

4심

AWG30

PTFE (현 설계: UL1213 계열)

기준 설계 길이 Lref

40 ±2 mm

절단/완성 길이 기준: 확인 필요
양단 숫자는 전기적 핀 번호입니다. 실제 커넥터 핀 위치·래치·키 방향을 나타내지 않습니다.

## 구성품

전선 | PTFE AWG30 | 4가닥; 선색 확인 필요
플러그 하우징 | JST SHR-04V-S | 1개
압착 콘택트 | JST SSH-003T-P0.2-H | 4개
맞물리는 PCB 헤더 | JST SM04B-SRSS-TB (J3) | PCB 장착품; 하네스 BOM 제외
납땜부 절연 | 개별 수축튜브 | 4개; 규격·절단 길이 확인 필요

## 제작 치수 확정 항목

Lcut: 전선 절단 길이 — 확인 필요

Lassy: 완성 길이 및 측정 기준점 — 확인 필요

양단 탈피·납땜 길이 — 확인 필요

압착 높이·폭·인장 기준 — 확인 필요

선색·수축튜브 규격 — 확인 필요

## 조립·검사 주기

HTX99R 뒤 핀 납땜 → 바디 통로·홀더 창 통과 → J3에 삽입.

커넥터 체결 중 플러그 끝은 자유롭게 두어 전선 꼬임을 방지.

실제 HTX99R 핀 번호·보는 방향과 대조 후 핀맵 승인.

전수 핀맵 도통·인접선 단락·단자 잠금·납땜부 절연을 확인. 시험 수치와 공구 조건은 해당 단자 사양 확정 후 기입.

도면번호 HMT500-W-001 | Rev A | 단위 mm | A3 / NTS | 1/3 · 작성: 설계 검토
