okchois/Oilinwater/hardware/mech/out/harness/HMT500_W-2_RevA.pdf

# HMT500 | W-2 M12 전원·통신·출력 하네스

제작 검토용 · Rev A · 기구 Rev I / PCB A5-R1 기준 · 2026-10-02

### 길이 기준·탈피·압착 조건 미확정 — 양산 제작 승인 도면 아님

## 전기 연결 개략도 (핀 배열도 아님 / 축척 없음)

M12 8P 뒤 납땜 단자 | JST GHR-08V-S → PCB J1
1 | 예비 / PCB NC | 1
2 | RS485_B_EXT | 2
3 | RS485_A_EXT | 3
4 | OUT1_EXT | 4
5 | OUT2_EXT | 5
6 | GND_IN | 6
7 | 예비 / PCB NC | 7
8 | VIN_EXT / 전원 + | 8

### 배선 사양

8심

AWG28

PTFE (현 설계: UL1213 계열)

기준 설계 길이 Lref

40 ±2 mm

절단/완성 길이 기준: 확인 필요
양단 숫자는 전기적 핀 번호입니다. 실제 커넥터 핀 위치·래치·키 방향을 나타내지 않습니다.

## 구성품

전선 | PTFE AWG28 | 8가닥; 선색 확인 필요
플러그 하우징 | JST GHR-08V-S | 1개
압착 콘택트 | JST SSHL-002T-P0.2 | 8개
맞물리는 PCB 헤더 | JST SM08B-GHS-TB (J1) | PCB 장착품; 하네스 BOM 제외
M12·납땜부 절연 | M12 품번 및 수축튜브 | 품번·치수·절단 길이 확인 필요

## 제작 치수 확정 항목

Lcut: 전선 절단 길이 — 확인 필요

Lassy: 완성 길이 및 측정 기준점 — 확인 필요

양단 탈피·납땜 길이 — 확인 필요

압착 높이·폭·인장 기준 — 확인 필요

선색·수축튜브 규격 — 확인 필요

## 조립·검사 주기

핀 n ↔ 핀 n 직결. 1·7번도 현 8심 하네스에 포함되며 PCB에서는 NC.

밀대로 J1에 삽입할 길이와 턴버클 체결 후 여유선 수납 공간을 함께 확보.

실제 M12 단자·수축튜브 확인 전 길이 축소 금지. 단자 정면/배선면 혼동 주의.

전수 핀맵 도통·인접선 단락·단자 잠금·납땜부 절연을 확인. 시험 수치와 공구 조건은 해당 단자 사양 확정 후 기입.

도면번호 HMT500-W-002 | Rev A | 단위 mm | A3 / NTS | 2/3 · 작성: 설계 검토
