okchois/Oilinwater/hardware/mech/out/harness/HMT500_W-3_RevA.pdf

# HMT500 | W-3 샤시 접지 하네스

제작 검토용 · Rev A · 기구 Rev I / PCB A5-R1 기준 · 2026-10-02

### 길이 기준·탈피·압착 조건 미확정 — 양산 제작 승인 도면 아님

## 전기 연결 개략도 (핀 배열도 아님 / 축척 없음)

PCB J5.1 납땜 | M2 비절연 링 단자 → 바디
1 | CHASSIS | M2 | 배선 사양
| | | 1심
| | | AWG28
| | | PTFE
| | | 녹/황 또는 녹색 (최종 색 확인)

기준 설계 길이 Lref

### 25 mm / 공차 확인 필요

| | | 절단/완성 길이 기준: 확인 필요
양단 숫자는 전기적 핀 번호입니다. 실제 커넥터 핀 위치·래치·키 방향을 나타내지 않습니다.

## 구성품

전선 | PTFE AWG28 | 1가닥
링 단자 | M2 비절연, AWG28 대응 | 1개; 제조사 품번 확인 필요
링 단자 외형 조건 | 바깥 Ø4.5 이하 / 두께 0.8 이하 | 현 기구 설계 조건
체결 위치 | 홀더 위쪽 축 나사 M2×8 | 금속 바디 탭과 전기 접촉
PCB 접속 | J5.1 납땜 | 신호 GND_IN과 혼동 금지

## 제작 치수 확정 항목

Lcut: 전선 절단 길이 — 확인 필요

Lassy: 완성 길이 및 측정 기준점 — 확인 필요

양단 탈피·납땜 길이 — 확인 필요

압착 높이·폭·인장 기준 — 확인 필요

선색·수축튜브 규격 — 확인 필요

## 조립·검사 주기

J5 납땜 → 홀더 위쪽 축 나사의 링 단자 → 금속 바디.

드라이버 접근 경로와 센서 하네스 창을 침범하지 않도록 수납.

링 중심 기준 완성 길이와 전선 절단 길이는 서로 다름. 단자 확정 후 치수화.

전수 핀맵 도통·인접선 단락·단자 잠금·납땜부 절연을 확인. 시험 수치와 공구 조건은 해당 단자 사양 확정 후 기입.

도면번호 HMT500-W-003 | Rev A | 단위 mm | A3 / NTS | 3/3 · 작성: 설계 검토
