okchois/Oilinwater/docs/reference/ist-mk33-study.md

# IST MK33 습도 센서 스터디 — 데이터시트·응용노트·백서 요약과 HMT500 반영 사항

작성일: 2026-09-29 · 원문 (두텍 제공, 저작권상 저장소에는 넣지 않음):
- DHMK33-W_E 2.4.0 — MK33-W 데이터시트 (4쪽)
- AH_E 2.4.0 — Application Note, Humidity Elements (7쪽: MK33, K5, P14, P14 Rapid, 취급·납땜·세척)
- iST White paper "Moisture in Oil" (6쪽, 2023/03)

## 1. MK33-W 데이터시트 핵심

| 항목 | 값 | HMT500에 주는 의미 |
|---|---|---|
| 크기 | 10.8 × 3.81 × 0.4 / 1.2 mm (SIL 선), 0.4 / 0.8 mm (Au/Cu 선) | mini판(5.0 × 3.81)이 캐리어에 맞음 → mini 유지 |
| 습도 범위 | 0–100 % RH, **최대 이슬점 +95 °C** | **고온에서 측정 상한이 줄어듦 (2절)** |
| 온도 범위 | −40 ~ +190 °C | 120 °C 목표에 충분 |
| 기준 용량 C30 | 300 pF ± 40 pF (30 % RH, 23 °C) | 개체 편차 ±13 % → **개별 교정 필수** |
| 감도 | 0.45 pF/% RH (15–90 % RH) | 0–100 % 전 범위 약 47 pF 변화 (284 → 331 pF, 곡선) |
| 손실계수 | < 0.01 (23 °C, 10 kHz, 90 % RH) | 측정 회로의 누설 영향 작음 |
| 직선성 | < 2 % RH (15–90 %, 1점 교정 후) | 저습 쪽이 가파른 곡선 → 다점 교정·다항 보정 권장 |
| 히스테리시스 | < 2 % RH | 정확도 예산의 큰 항목 |
| 응답 t63 | < 6 s (50 → 0 % RH, 23 °C, 공기) | 오일 속에서는 오일 확산이 지배 (4절) |
| 온도 의존성 (공칭) | ΔRH = (B1·RH + B2)·T + (B3·RH + B4). B1 = 0.0011 /°C, B2 = 0.0892 %RH/°C, B3 = −0.0268, B4 = −2.079 %RH | **보정 없으면 오차가 큼** (3절) |
| **측정 신호** | **교류, DC 바이어스 없음, 1–100 kHz (권장 10 kHz), < 12 Vpp** | **PCAP04 구동 방식 확인 필요 (5절, 가장 중요)** |
| 접속 | CuP-SIL 선 Sn 도금 10 mm / Au/Cu 선 Ø0.4 10 mm / Au/Cu 12 mm PTFE 절연 + 실리콘 글롭탑 | 오일 침지 → **PTFE 절연 + 글롭탑판(151306 계열)** 이 유리 |
| 주문 코드 | 150474 MK33 SIL, 150468 MK33-W Au/Cu, 151306 MK33-W HMN300-40.1138.W.012.S (PTFE + 글롭탑) | **MK33-W mini = 150138** (백서) |

## 2. 허용 온습도 범위 — 고온에서 aw 상한

데이터시트의 허용 범위 그래프는 **이슬점 95 °C(수증기압 84.6 kPa)** 가 한계입니다. 95 °C를 넘으면 측정할 수 있는 최대 aw가 줄어듭니다.

| 오일 온도 | 80 °C | 95 °C | 100 °C | 105 °C | 110 °C | **120 °C** | 130 °C |
|---|---|---|---|---|---|---|---|
| 허용 최대 aw | 1.0 | 1.0 | 0.83 | 0.70 | 0.59 | **0.43** | 0.31 |

(포화 수증기압 IAPWS 근사로 계산. 그래프 판독값과 일치)

→ **HMT500 사양 표기:** "aw 0–1 (오일 ≤ 95 °C), 95 °C 초과 시 이슬점 95 °C 이하 범위". 120 °C에서는 aw 0.43까지만 보장됩니다. EE364도 ppm 출력을 0–100 °C에서만 유효하다고 합니다. 펌웨어에서 이 한계를 넘으면 상태 비트와 알람을 켭니다.

## 3. 온도 의존성 보정 (펌웨어)

공칭 식으로 계산한 온도 영향 (23 °C 기준에서 거의 0):

| 온도 | RH 20 % | RH 50 % | RH 80 % |
|---|---|---|---|
| 60 °C | +4.1 % RH | +5.2 | +6.4 |
| 100 °C | +8.5 | +11.0 | +13.5 |
| 120 °C | +10.7 | +13.9 | +17.0 |

- 보정하지 않으면 100 °C에서 **10 % RH 이상** 틀어집니다. 그래서 펌웨어에 이 식을 넣습니다(부호 규약은 IST에 확인).
- 공칭 식이므로, 양산은 **2온도 이상 교정**(예: 25 °C와 80 °C)으로 개체별 계수를 구합니다.
- 측정하는 온도는 습도 센서 바로 옆 Pt1000(MiniSens) 값을 씁니다([온도 센서 선정](../hw/temperature-sensor-selection.md)).

## 4. 백서 — 오일 수분 측정의 원리와 주의점

- **측정 원리:** 오일 속 물이 다공성 윗전극을 지나 고분자층으로 확산되고, 그 물의 양이 정전용량을 바꿉니다. 공기 중과 원리가 같지만, 고온과 첨가제·화학물질 때문에 조건이 가혹합니다.
- **MK33은 오일 수분용으로 특화된 센서입니다.** 다만 상용 오일에는 공개되지 않은 첨가제가 있어서, **오일마다 센서 적합성 평가를 권장**합니다.
- **% RH(aw)가 ppm보다 운전 판단에 낫습니다.** 오일이 노화되면 물 용해도가 바뀝니다. 백서 예시에서는 포화량이 5,000 → 4,000 ppm으로 떨어지면 같은 60 % RH가 3,000 → 2,400 ppm이 됩니다. aw 경보는 노화를 자동 반영하지만 ppm 경보는 여유가 줄어듭니다.
  → HMT500 기본 출력: **OUT1 = aw** (EE364와 같음), ppm은 오일 계수(A, B) 기반 보조 출력. 설정 도구에 이 설명을 넣습니다.
- **평형 시간:** 물이 오일에 고르게 녹는 데는 시간이 걸리고(교반해도 수 시간), 센서 응답보다 훨씬 느립니다. **설치 위치(유동이 있는 곳)** 가 측정 품질을 좌우합니다 → 설치 가이드에 반영.
- **장기 안정성:** 에스테르유·광유에서 장기 측정 결과가 안정적입니다(실온). 변압기 호흡처럼 주위 공기와의 교환이 수분 변동을 만듭니다.
- **관련 IST 제품:** MK33-W mini (150138), HYT 271 모듈 (153382, 공장 교정, I²C), Moisture in oil 프로브 (155958, 완제품).

## 5. 측정 회로 — PCAP04와 "DC 바이어스 없는 교류" 요구 (확인 필요)

- 데이터시트는 **DC 바이어스 없는 교류 신호**로 측정하라고 합니다. 고분자에 DC가 계속 걸리면 물 분자가 이온처럼 이동(분극·전기분해)해 드리프트와 수명 저하가 생길 수 있습니다.
- PCAP04는 센서를 충전 후 저항으로 방전시키는 **방전시간 방식**입니다. 단순 접지형(grounded) 연결에서는 센서에 한 방향 전압이 걸려 평균 DC가 남을 수 있습니다.
- **대책 (우선순위):**
  1. PCAP04를 **플로팅 차동 모드**로 쓰고, 충방전 방향이 번갈아 바뀌는 설정(보상 모드)으로 센서 양단 평균 전압을 0으로 만드는지 ScioSense 자료로 확인
  2. 측정 순간에만 짧게 구동하고 나머지 시간은 센서 양단을 같은 전위로 둠 (듀티 최소화)
  3. 위가 안 되면 10 kHz 교류 구동 + 동기 검파(또는 IST가 쓰는 방식의 전용 ASIC, HYT 모듈)로 변경
- → PCAP04 데이터시트(요청 중) 확인 후 회로를 확정합니다. **미결 사항에 추가.**

## 6. 취급·납땜·세척 (생산 공정 지침에 반영)

| 구분 | IST 지침 |
|---|---|
| 취급 | 활성 면을 만지지 않음. 장갑 필수. **플라스틱 핀셋으로 가장자리나 선만** 잡음 (금속 핀셋 금지). 굽힘·긁힘 금지. UV 노출 금지 |
| 보관 | 원래 블리스터에만, −20 ~ +50 °C |
| 납땜 | 인두 최대 320 °C, 선 끝에서 10 s 이내. 활성 면에 플럭스 잔사 금지 |
| 접착 | 접착제로 고정하면 80 °C × 1 h 베이킹 |
| **교정 시점** | **납땜 후 최소 5일 경과 후 교정** (열 이완 시간) → 생산 일정에 반영 |
| 세척 | 상온 이소프로판올 (약한 초음파 가능) 후 건조. 면봉 등 기계적 세척 금지. 먼지는 오일 없는 여과 공기 |

## 7. HMT500 반영 목록

| # | 항목 | 반영 |
|---|---|---|
| 1 | 센서 품번 | MK33-W mini (150138). 오일 침지를 고려해 PTFE 절연 + 글롭탑 사양을 IST에 문의 (151306의 mini판) |
| 2 | 사양서 | aw 0–1 (≤ 95 °C), 95 °C 초과 시 이슬점 95 °C 한계 (120 °C에서 aw ≤ 0.43) |
| 3 | 펌웨어 | 온도 의존성 보정식 + 개체별 교정 계수, 한계 초과 알람, aw 기본 출력 |
| 4 | 측정 회로 | PCAP04의 DC 바이어스 없는 구동 확인 (5절) — **회로 확정 전 필수** |
| 5 | 교정 | 다점 RH × 2온도 이상, 납땜 후 5일 이후 |
| 6 | 생산 | 6절 취급 지침을 작업 표준서로 |
| 7 | 적용 | 고객 오일별 적합성 시험 절차, 설치 위치 가이드 (유동부) |
