okchois/Oilinwater/hardware/mech/out/assembly_procedure/overview.png

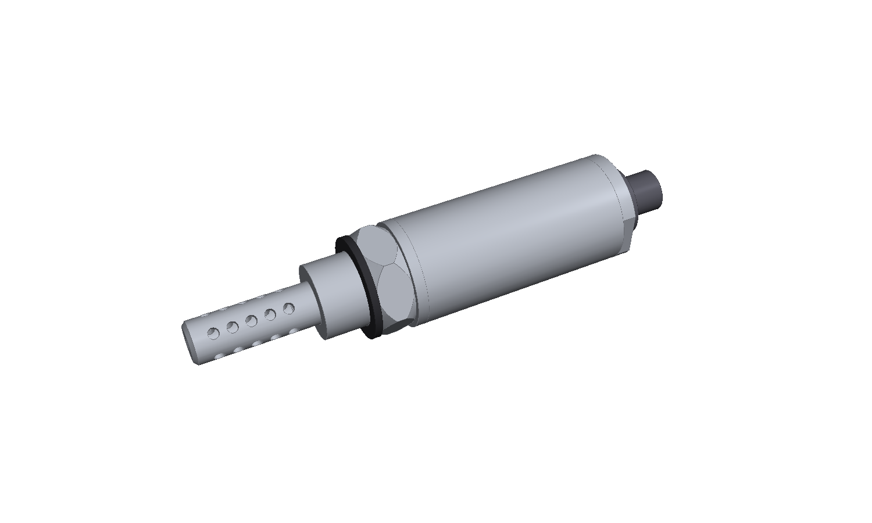
hardware/mech/out/assembly_procedure/overview.png
