okchois/Oilinwater/hardware/mech/out/studio/HMT500_studio_02_rear.png

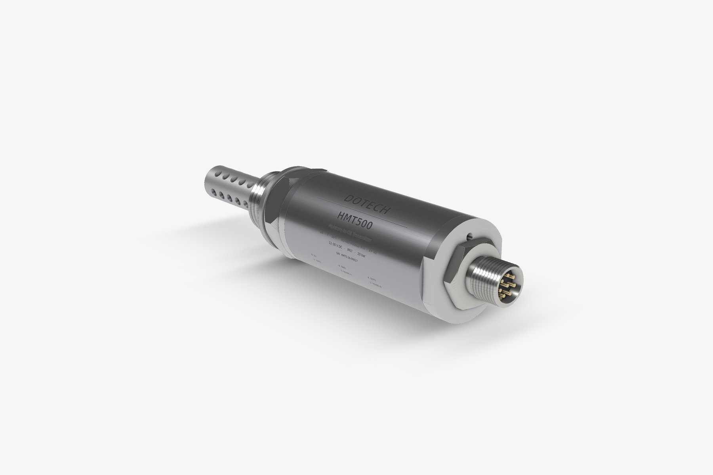
hardware/mech/out/studio/HMT500_studio_02_rear.png
