okchois/Oilinwater/hardware/mech/out/studio/HMT500_studio_03_side.png

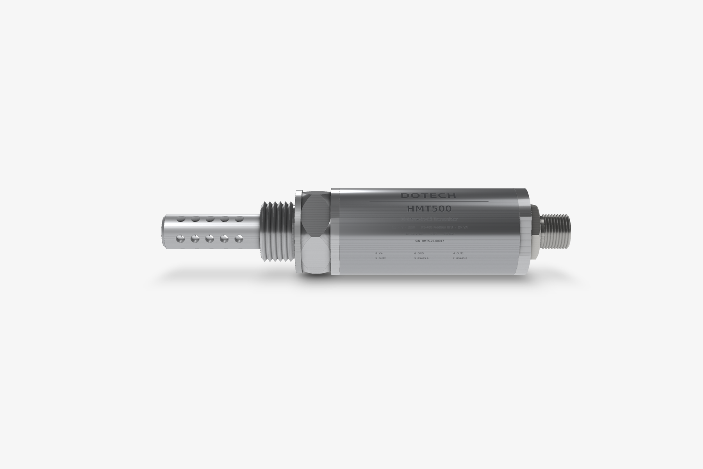
hardware/mech/out/studio/HMT500_studio_03_side.png
