okchois/Oilinwater/hardware/mech/out/studio/HMT500_studio_04_probe_closeup.png

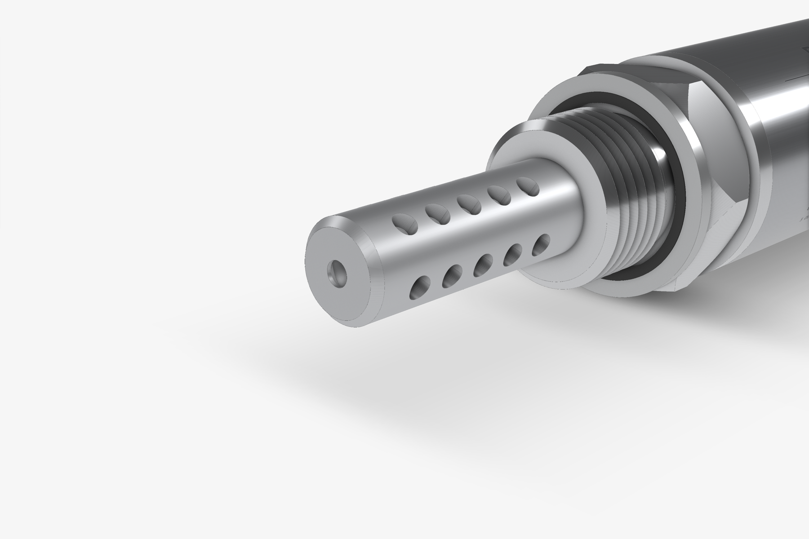
hardware/mech/out/studio/HMT500_studio_04_probe_closeup.png
