okchois/Oilinwater/hardware/mech/out/studio/HMT500_studio_05_top.png

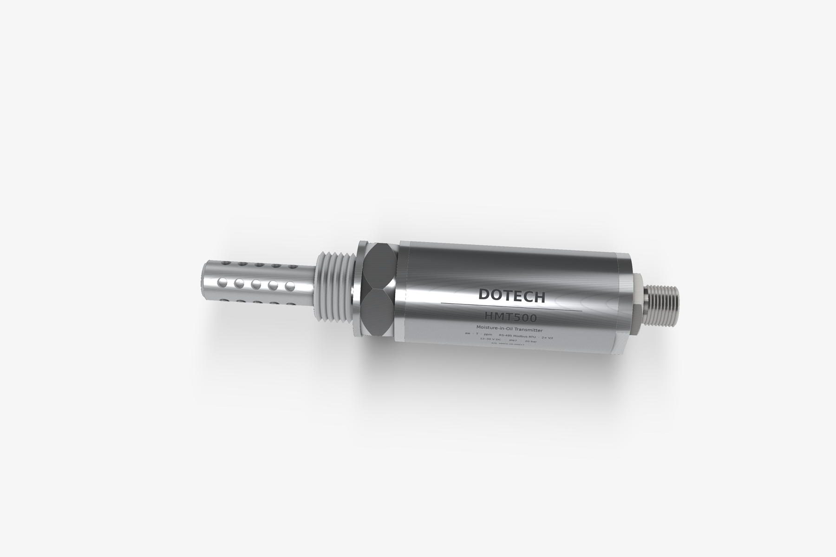
hardware/mech/out/studio/HMT500_studio_05_top.png
