okchois/Oilinwater/manufacturing/jlc/lcsc/order_lcsc_harness.csv

Harness | Description | Qty/set | LCSC P/N
W-1 | JST SHR-04V-S (SH 1.0 mm 4P 하우징) | 1 | C385125
W-1 | JST SSH-003T-P0.2-H (SH 콘택트, AWG 32–28) | 4 | C263995
W-2 | JST GHR-08V-S (GH 1.25 mm 8P 하우징) | 1 | C485357
W-2 | JST SSHL-002T-P0.2 (GH 콘택트, AWG 30–26) | 8 | C189897
W-1 | PTFE 절연선 AWG 30 (UL1213 계열, 200 °C) | 4 × 40 mm | (조회 후 기입)
W-2 | PTFE 절연선 AWG 28 (UL1213 계열) | 8 × 40 mm | (조회 후 기입)
W-3 | PTFE 절연선 AWG 28 녹/황 또는 녹색 | 1 × 25 mm | (조회 후 기입)
W-3 | M2 링 단자, 비절연, AWG 28–22, 바깥 Ø4.5 이하, 두께 0.8 이하 | 1 | (조회 후 기입)
