okchois/Oilinwater/manufacturing/jlc/jlcmc/order_jlcmc.csv

Item | Description | Qty/set | Qty total | Use | JLCMC P/N
P-207a | M2×6 나사, A4-70, ISO 14580 (치즈머리 Torx) 또는 ISO 7380 | 1 | 1 | 홀더 → 바디 (아래) | (검색 후 기입)
P-207b | M2×8 나사, A4-70, ISO 14580 | 1 | 1 | 홀더 → 바디 (위, 샤시 링 단자 함께) | (검색 후 기입)
P-207c | M2×12 나사, A4-70, ISO 14580 | 2 | 2 | PCB → 홀더 가로 고정 (벤치) | (검색 후 기입)
P-210 | M3×3 무두나사 (ISO 4026 평끝), A4 | 2 | 2 | 엔드캡 몰딩 구멍 막음 (+ 실런트) | (검색 후 기입)
P-205 | O링 24 × 1.5, FKM 75 (Rev H) | 2 | 2 | 바디–하우징, 하우징–엔드캡 (반경 방향) | (검색 후 기입)
P-208 | O링 8 × 1.2, FKM 75 | 1 | 1 | HTX99R 커넥터 | (검색 후 기입)
P-203 | 본디드 씰 G1/2 (21.5 × 28.7 × 2, 강 + FKM) | 1 | 1 | 설치 나사 밀봉 — JLCMC에 없으면 유압 부품상 | (검색 후 기입)
