okchois/Oilinwater/manufacturing/jlc/artwork_A5_R2_review/레퍼런스_배치목록.csv

Reference | 표시 | X_mm | Y_mm | Angle_deg | Width_mm | Height_mm | Stroke_mm | 지시선
C1 | 인쇄 | 146.72190500000002 | 98.9 | 0 | 0.5 | 0.8 | 0.1 | False
C12 | 인쇄 | 133.71 | 94.82619 | 90 | 0.5 | 0.8 | 0.1 | True
C13 | 인쇄 | 138.45000000000002 | 94.11619 | 90 | 0.5 | 0.8 | 0.1 | True
C14 | 인쇄 | 122.17649999999999 | 97.89 | 90 | 0.5 | 0.8 | 0.1 | False
C15 | 인쇄 | 125.7235 | 98.415 | 90 | 0.5 | 0.8 | 0.1 | False
C16 | 인쇄 | 112.52499999999999 | 108.6835 | 0 | 0.5 | 0.8 | 0.1 | False
C18 | 인쇄 | 124.125 | 92.7165 | 0 | 0.5 | 0.8 | 0.1 | False
C2 | 인쇄 | 121.0 | 102.9415 | 0 | 0.4 | 0.6 | 0.1 | False
C20 | 인쇄 | 127.12349999999999 | 99.415 | 90 | 0.5 | 0.8 | 0.1 | True
C21 | 인쇄 | 122.12349999999999 | 102.61 | 90 | 0.4 | 0.6 | 0.1 | False
C22 | 인쇄 | 121.23349999999999 | 89.785 | 90 | 0.5 | 0.8 | 0.1 | False
C23 | 인쇄 | 111.62380999999999 | 108.03499999999998 | 0 | 0.5 | 0.8 | 0.1 | True
C24 | 인쇄 | 125.8835 | 93.92500000000001 | 90 | 0.5 | 0.8 | 0.1 | False
C25 | 인쇄 | 114.4165 | 91.125 | 90 | 0.5 | 0.8 | 0.1 | False
C26 | 인쇄 | 145.29 | 93.0485 | 0 | 0.5 | 0.8 | 0.1 | False
C27 | 인쇄 | 129.9835 | 106.085 | 90 | 0.5 | 0.8 | 0.1 | False
C29 | 인쇄 | 114.7065 | 94.285 | 90 | 0.5 | 0.8 | 0.1 | False
C3 | 인쇄 | 107.45 | 103.47190499999999 | 90 | 0.5 | 0.8 | 0.1 | False
C30 | 인쇄 | 132.559999 | 108.184048 | 90 | 0.4 | 0.6 | 0.1 | True
C36 | 인쇄 | 141.3185 | 108.00999999999999 | 90 | 0.5 | 0.8 | 0.1 | False
C40 | 인쇄 | 127.29 | 101.1265 | 0 | 0.5 | 0.8 | 0.1 | True
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
U3 | 인쇄 | 144.43999999999997 | 90.535 | 0 | 0.5 | 0.8 | 0.1 | False
U4 | 인쇄 | 122.56 | 99.89999999999999 | 0 | 0.5 | 0.8 | 0.1 | False
U5 | 인쇄 | 122.3 | 96.49000000000001 | 90 | 0.5 | 0.8 | 0.1 | False
U6 | 인쇄 | 123.15 | 104.32 | 90 | 0.5 | 0.8 | 0.1 | True
U7 | 인쇄 | 122.96999999999998 | 108.95 | 0 | 0.5 | 0.8 | 0.1 | False
U8 | 인쇄 | 139.52999999999997 | 89.95 | 0 | 0.5 | 0.8 | 0.1 | False
U9 | 인쇄 | 133.399999 | 102.61 | 90 | 0.4 | 0.6 | 0.1 | True
C28 | 공간 부족으로 미표시
C4 | 공간 부족으로 미표시
C44 | 공간 부족으로 미표시
C45 | 공간 부족으로 미표시
C48 | 공간 부족으로 미표시
C50 | 공간 부족으로 미표시
C55 | 공간 부족으로 미표시
D51 | 공간 부족으로 미표시
FB1 | 공간 부족으로 미표시
R14 | 공간 부족으로 미표시
R19 | 공간 부족으로 미표시
R31 | 공간 부족으로 미표시
R51 | 공간 부족으로 미표시
R52 | 공간 부족으로 미표시
R9 | 공간 부족으로 미표시
U13 | 공간 부족으로 미표시
U15 | 공간 부족으로 미표시
U2 | 공간 부족으로 미표시
