okchois/Oilinwater/manufacturing/jlc/jlccnc/HMT500-M-103_housing_SUS316L.step

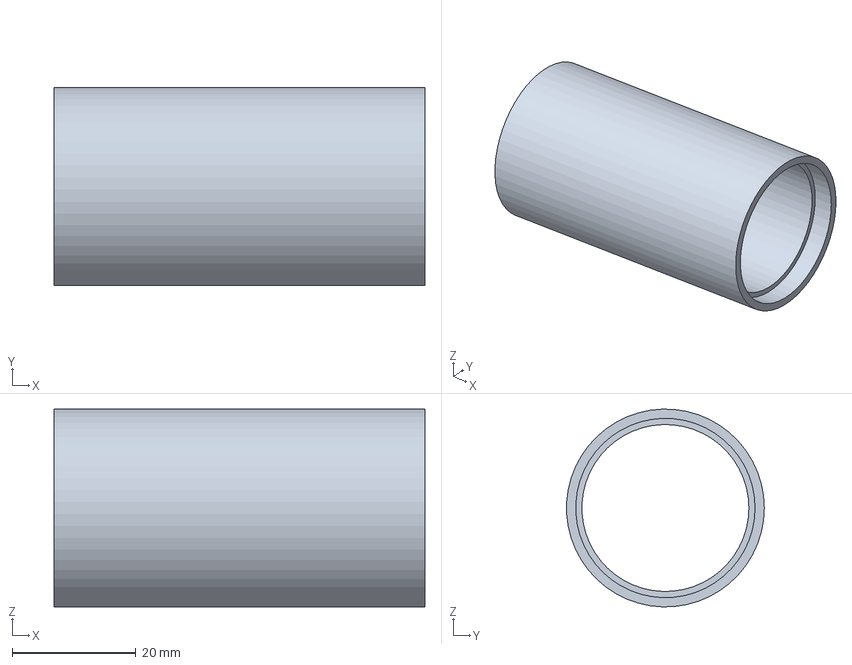
[picture p42: CAD file, 2026-09-30]
manufacturing/jlc/jlccnc/HMT500-M-103_housing_SUS316L.step
60.0 x 32.0 x 32.0 mm
