okchois/Oilinwater/manufacturing/jlc/jlccnc/HMT500-M-104_endcap_SUS316L.step

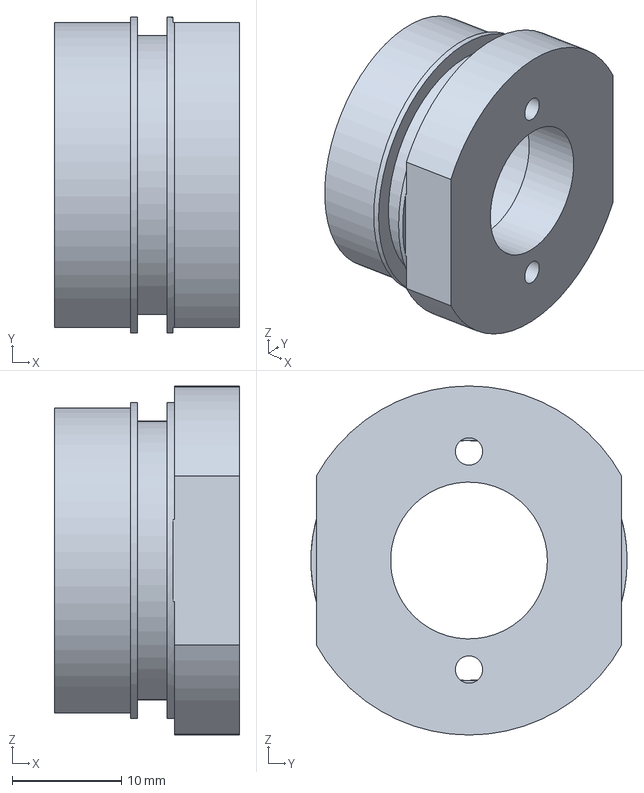
[picture p43: CAD file, 2026-09-30]
manufacturing/jlc/jlccnc/HMT500-M-104_endcap_SUS316L.step
17.0 x 29.0 x 32.0 mm
