okchois/Oilinwater/hardware/mech/out/assembly_procedure/step_01.png

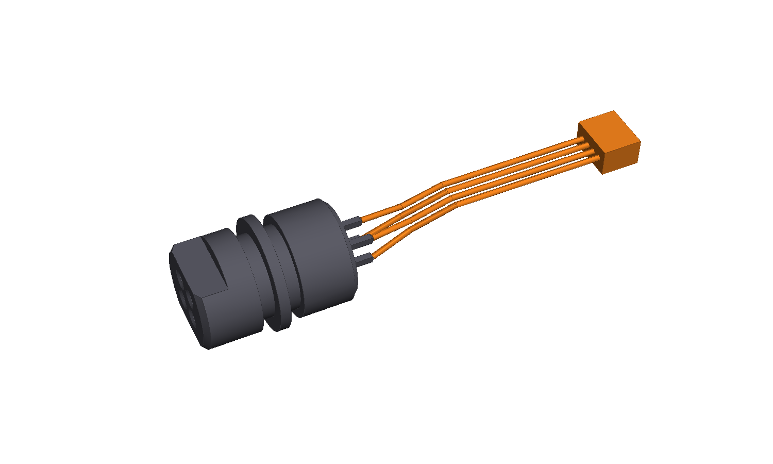
hardware/mech/out/assembly_procedure/step_01.png
