okchois/Oilinwater/hardware/mech/out/assembly_procedure/step_02.png

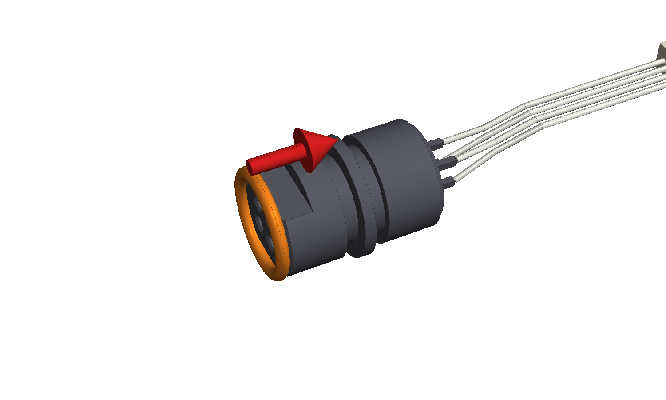
hardware/mech/out/assembly_procedure/step_02.png
