okchois/Oilinwater/hardware/mech/out/assembly_procedure/step_03.png

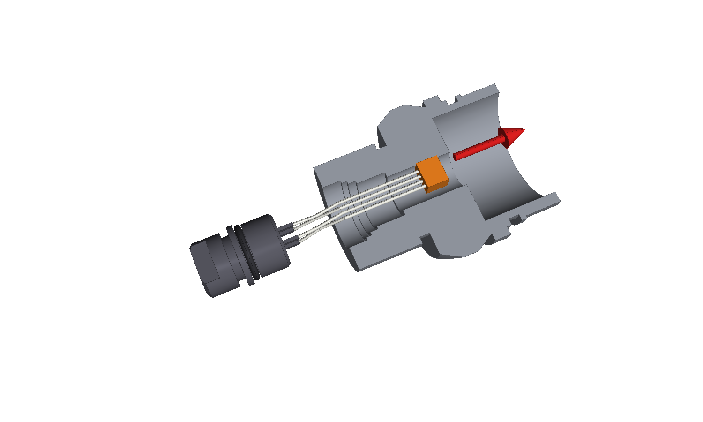
hardware/mech/out/assembly_procedure/step_03.png
