okchois/Oilinwater/hardware/mech/out/assembly_procedure/step_05.png

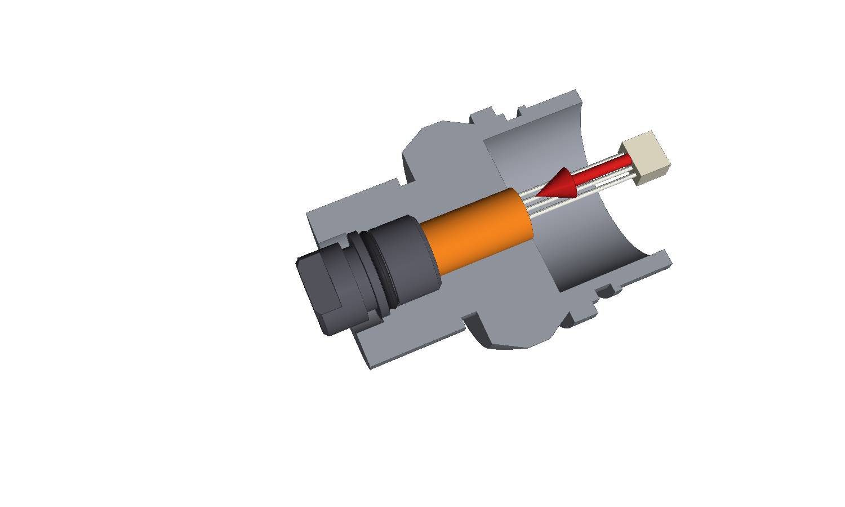
hardware/mech/out/assembly_procedure/step_05.png
