okchois/Oilinwater/hardware/mech/out/assembly_procedure/step_06.png

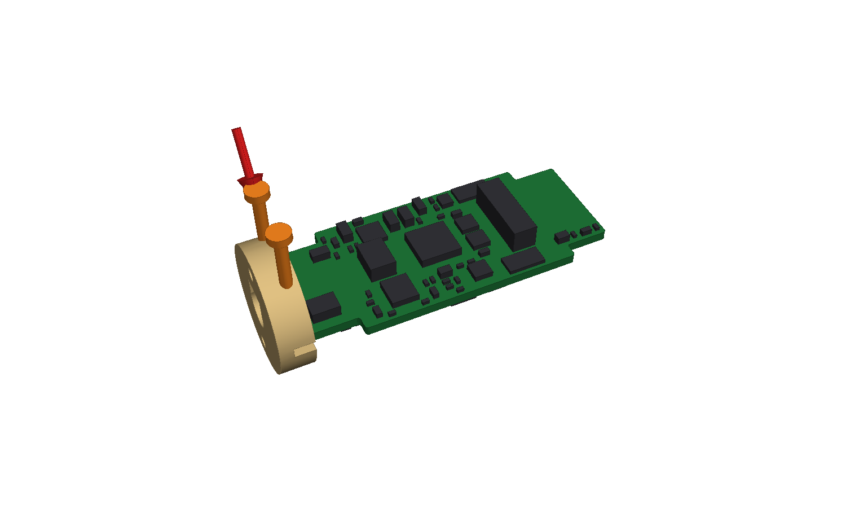
hardware/mech/out/assembly_procedure/step_06.png
