okchois/Oilinwater/hardware/mech/out/assembly_procedure/step_07.png

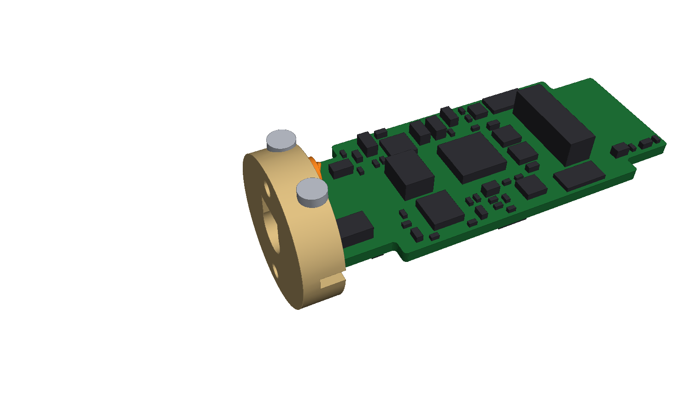
hardware/mech/out/assembly_procedure/step_07.png
