okchois/Oilinwater/hardware/mech/out/assembly_procedure/step_08.png

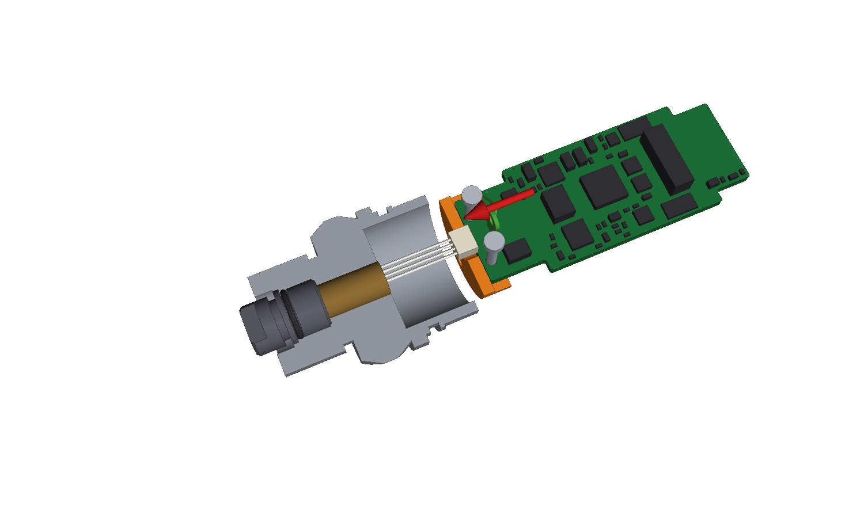
hardware/mech/out/assembly_procedure/step_08.png
