okchois/Oilinwater/hardware/mech/out/assembly_procedure/step_09.png

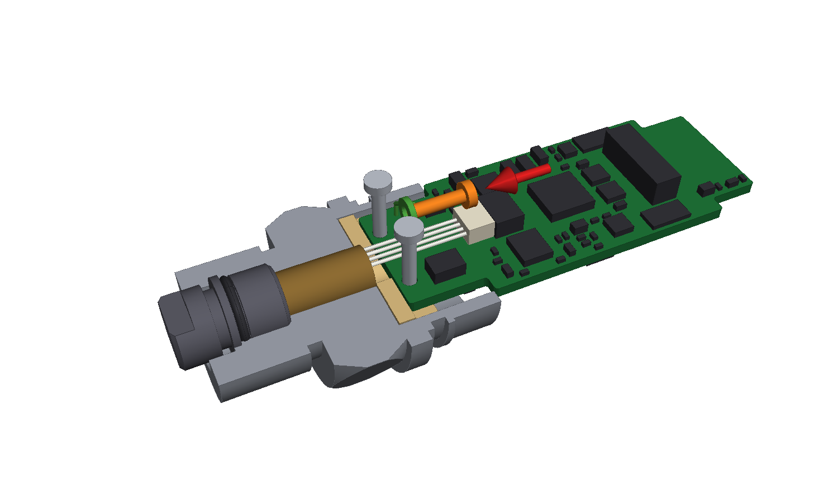
hardware/mech/out/assembly_procedure/step_09.png
