okchois/Oilinwater/hardware/mech/out/assembly_procedure/step_11.png

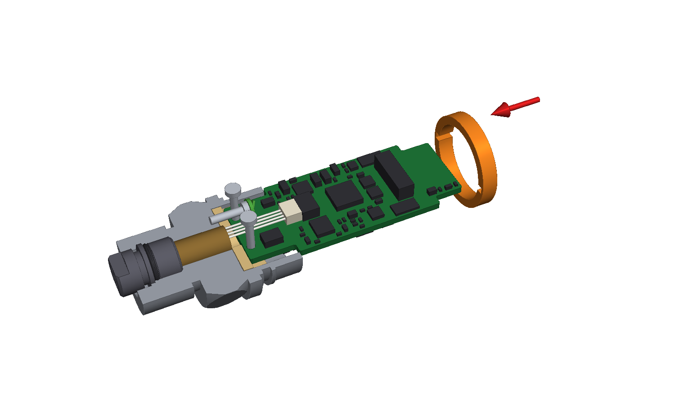
hardware/mech/out/assembly_procedure/step_11.png
