okchois/Oilinwater/hardware/mech/out/assembly_procedure/step_12.png

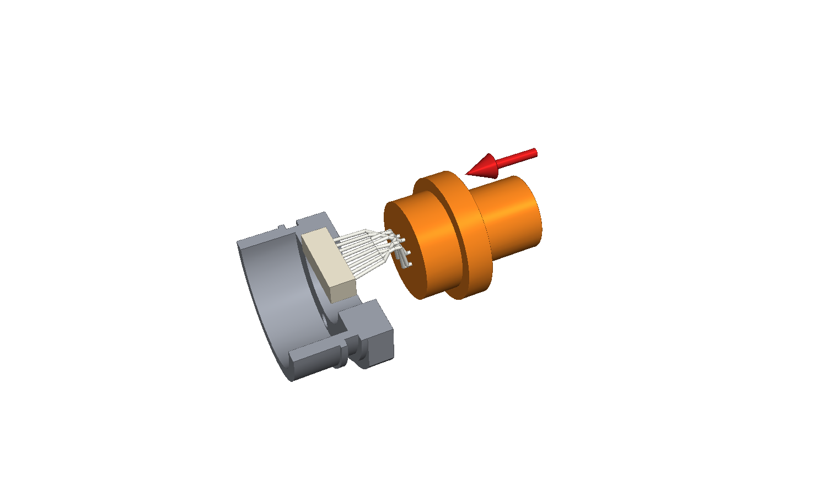
hardware/mech/out/assembly_procedure/step_12.png
