okchois/Oilinwater/hardware/mech/out/assembly_procedure/step_14.png

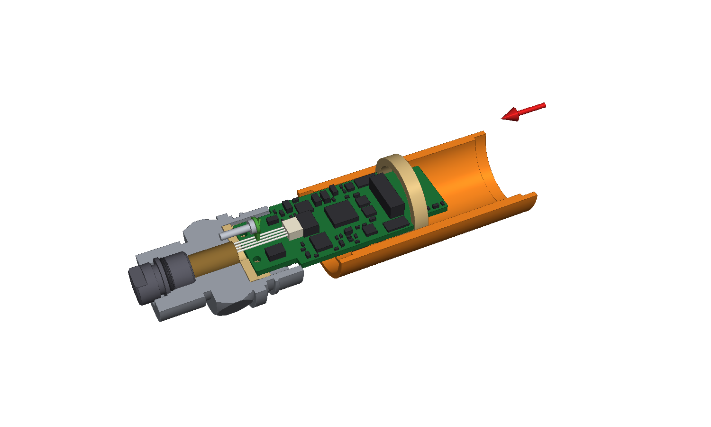
hardware/mech/out/assembly_procedure/step_14.png
