okchois/Oilinwater/hardware/mech/out/assembly_procedure/step_18.png

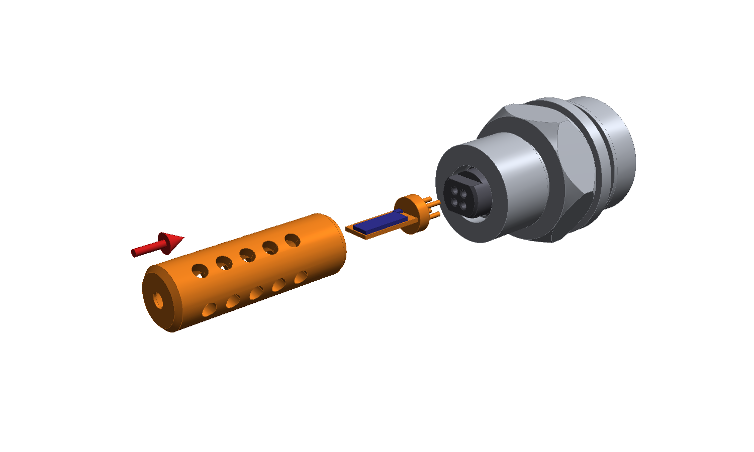
hardware/mech/out/assembly_procedure/step_18.png
