okchois/Oilinwater/hardware/mech/out/assembly_sim/assembled_bottom.png

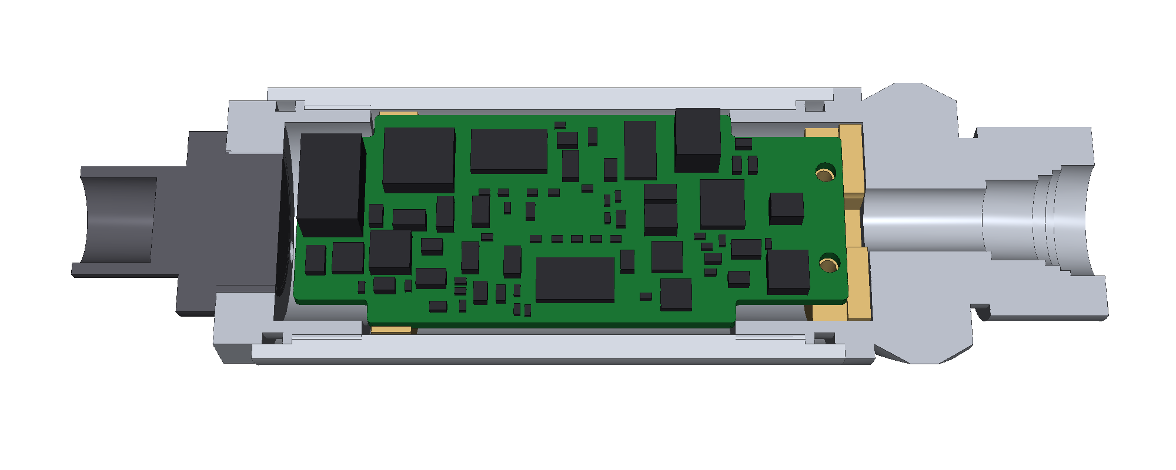
hardware/mech/out/assembly_sim/assembled_bottom.png
