okchois/Oilinwater/hardware/mech/out/assembly_sim/assembled_top.png

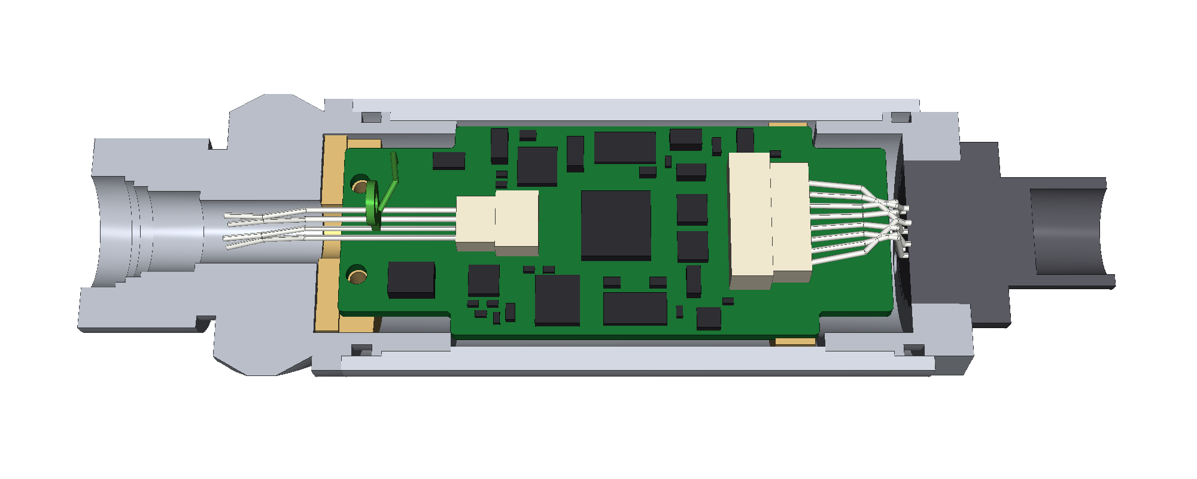
hardware/mech/out/assembly_sim/assembled_top.png
