okchois/Oilinwater/hardware/mech/out/assembly_sim/assembly_issues.png

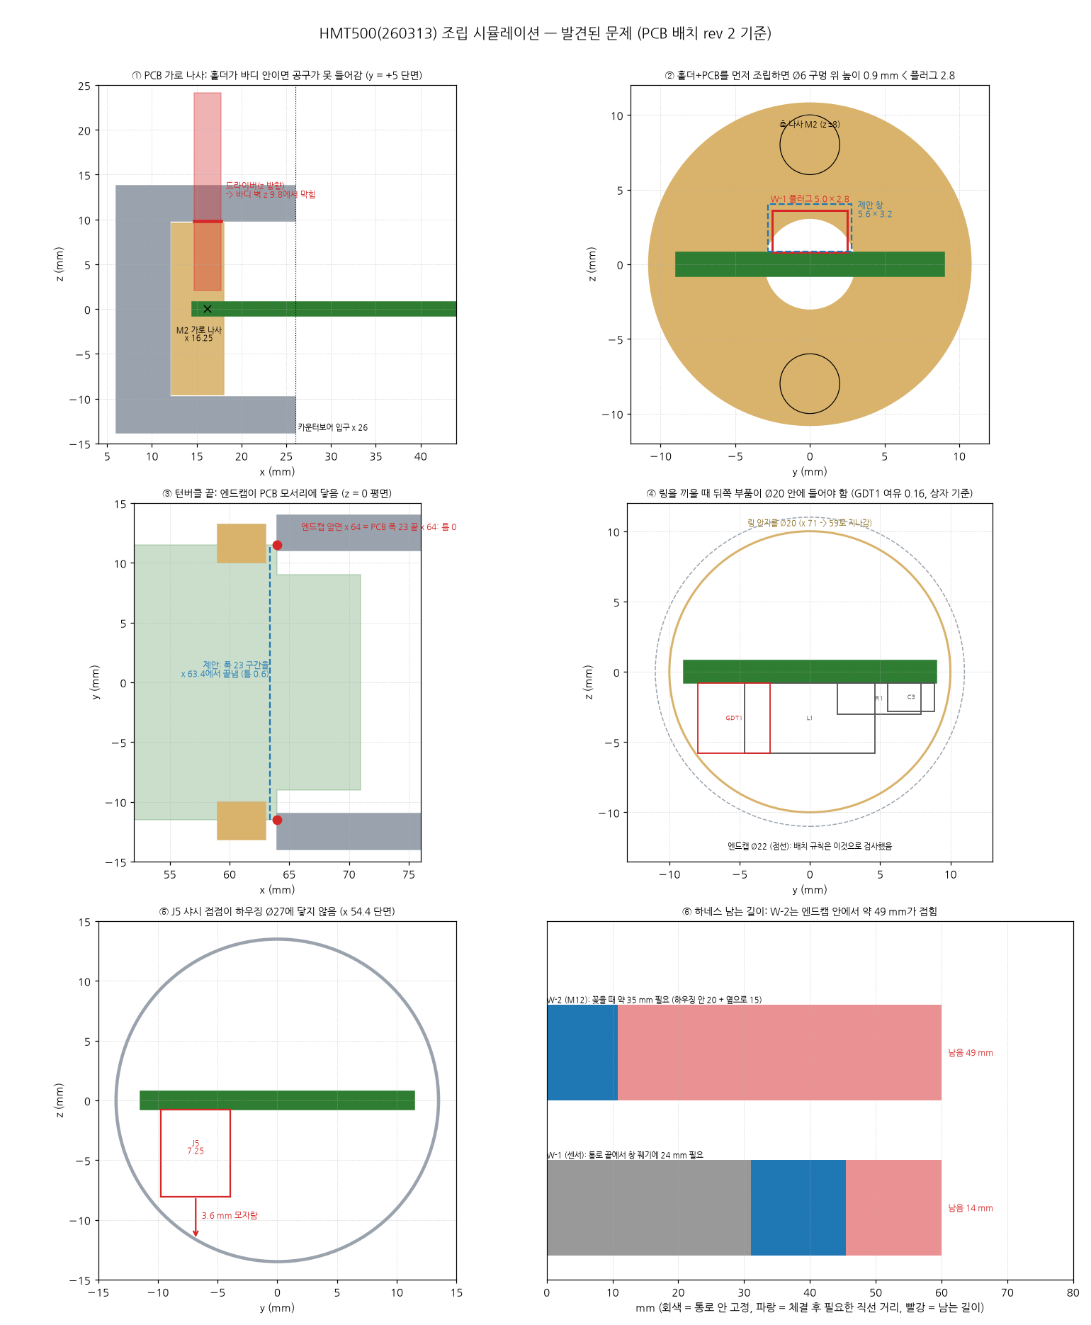
hardware/mech/out/assembly_sim/assembly_issues.png
