okchois/Oilinwater/hardware/mech/out/assembly_sim/assembly_fixes.png

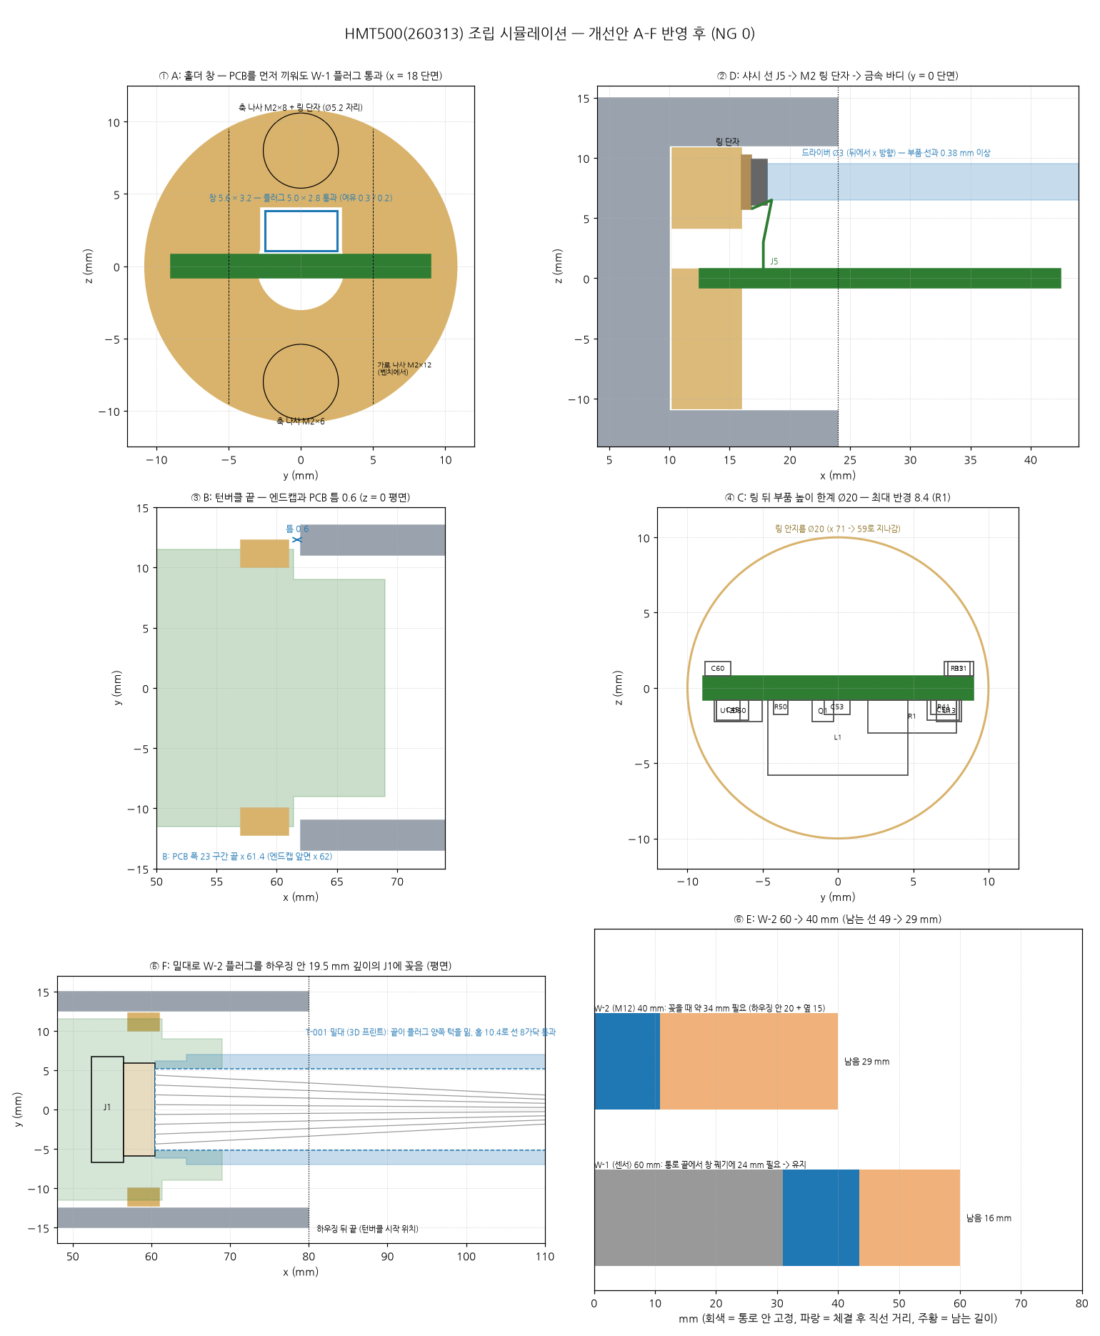
hardware/mech/out/assembly_sim/assembly_fixes.png
