okchois/Oilinwater/manufacturing/jlc/artwork_A5_R2_review/HMT500_A5-R2_TOP_BOTTOM.pdf

## HMT500 A5-R2 / TOP / ACTUAL PCB SILKSCREEN

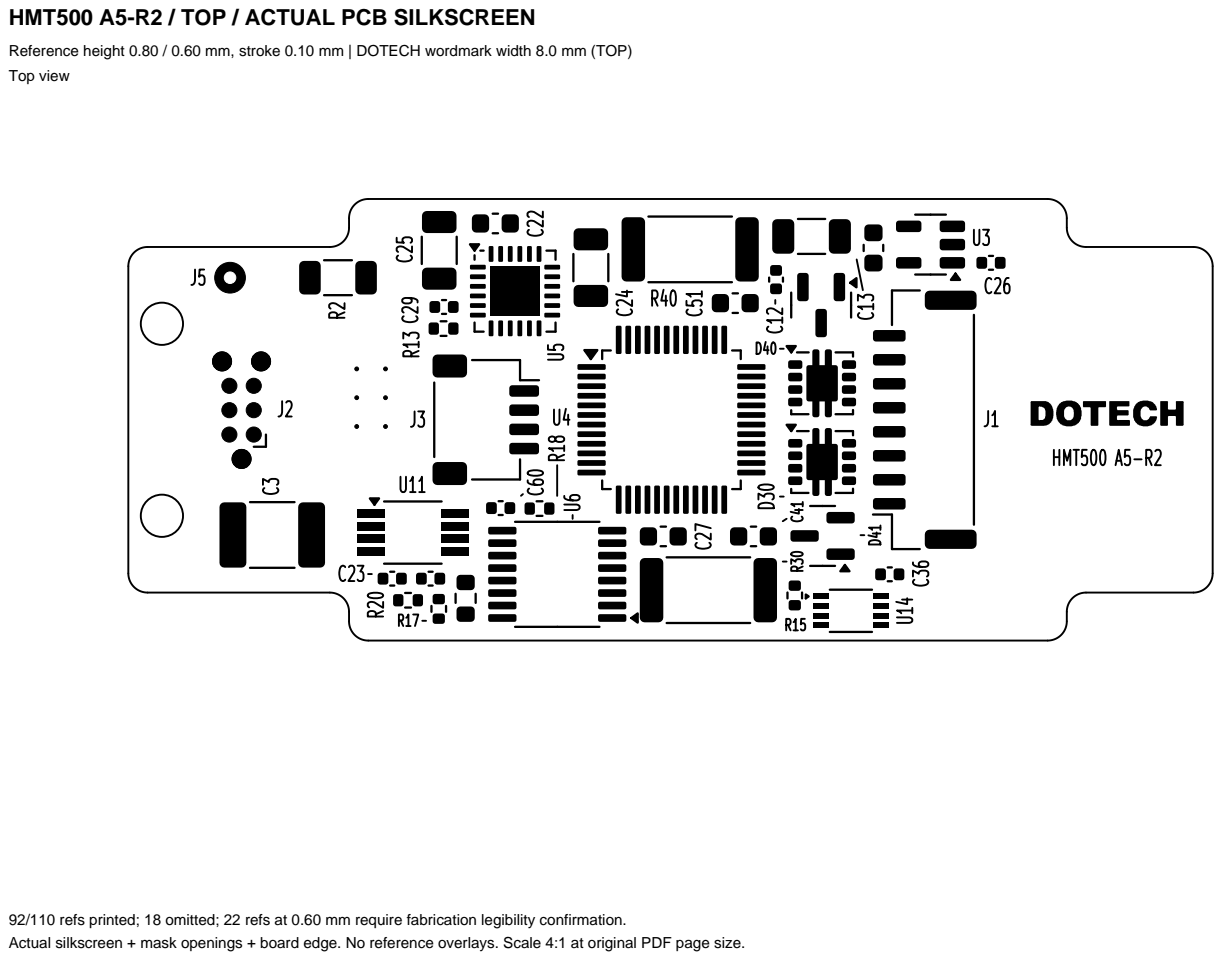
[picture p81: page 1]

Reference height 0.80 / 0.60 mm, stroke 0.10 mm | DOTECH wordmark width 8.0 mm (TOP)
Top view

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

## HMT500 A5-R2 / BOTTOM / ACTUAL PCB SILKSCREEN

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
